ZeshuLiu/PolaMiyaHardware/结构Rev2N/电路/机身主控/TSSOP-14_4.4x5mm_P0.65mm.SLDASM

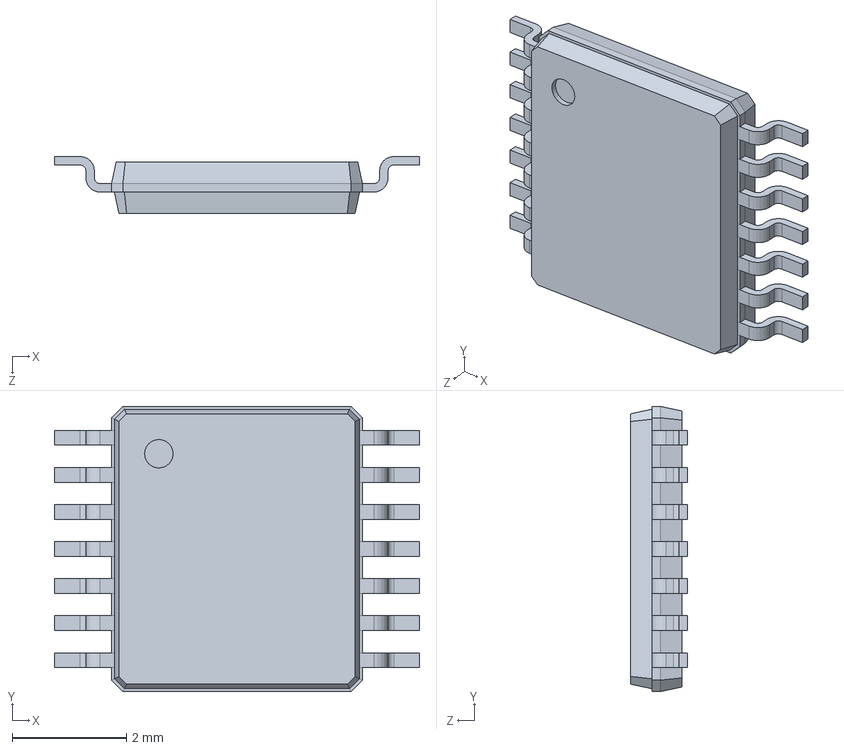
[picture p2: CAD file, 2025-09-27]
结构Rev2N/电路/机身主控/TSSOP-14_4.4x5mm_P0.65mm.SLDASM
6.40 x 5.00 x 1.00 mm
