ZeshuLiu/PolaMiyaHardware/结构Rev2N/电路/机身主控/VSSOP-8_3.0x3.0mm_P0.65mm.SLDASM

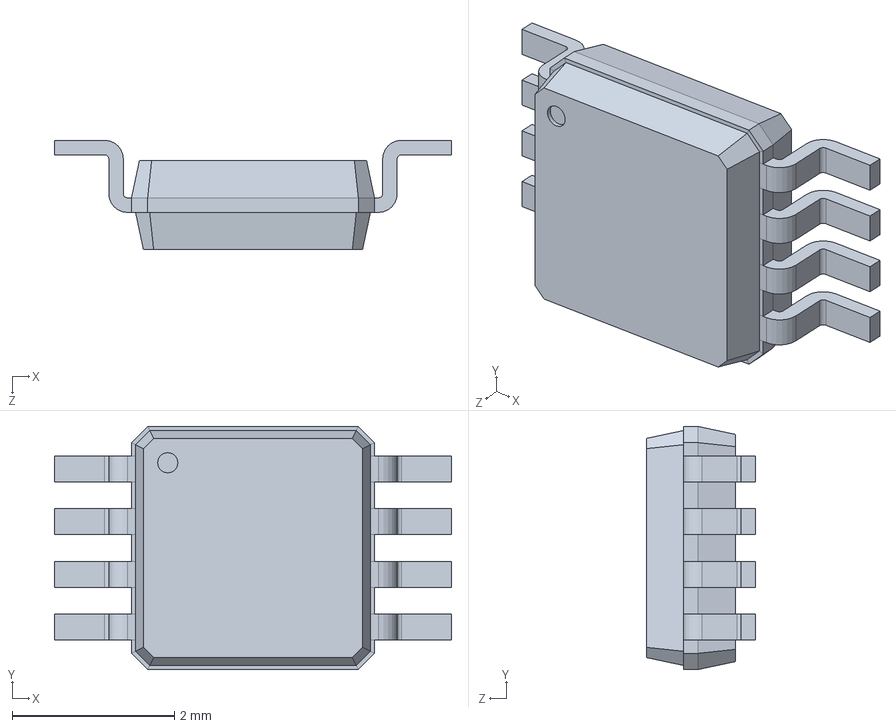
[picture p5: CAD file, 2025-09-27]
结构Rev2N/电路/机身主控/VSSOP-8_3.0x3.0mm_P0.65mm.SLDASM
4.90 x 3.00 x 1.35 mm
