ZeshuLiu/PolaMiyaHardware/电路/闪光灯转接/FlashAdapter/upper.SLDPRT

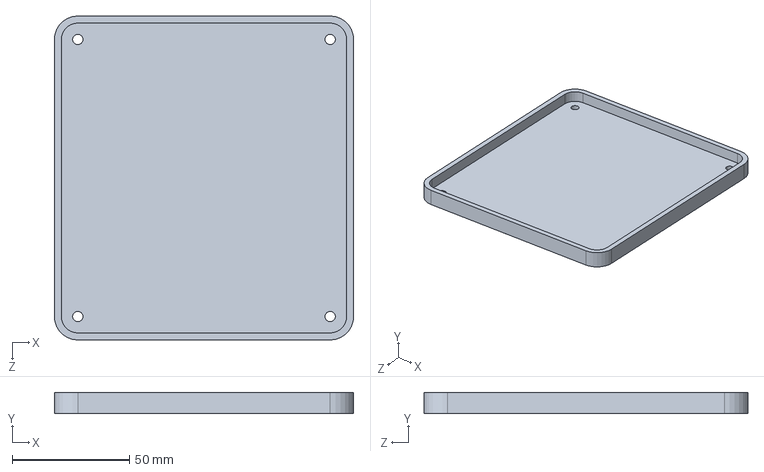
[picture p7: CAD file, 2025-12-25]
电路/闪光灯转接/FlashAdapter/upper.SLDPRT
127.5 x 9.00 x 138.0 mm
