ZeshuLiu/PolaMiyaHardware/结构Rev2N/外壳/顶壳.SLDPRT

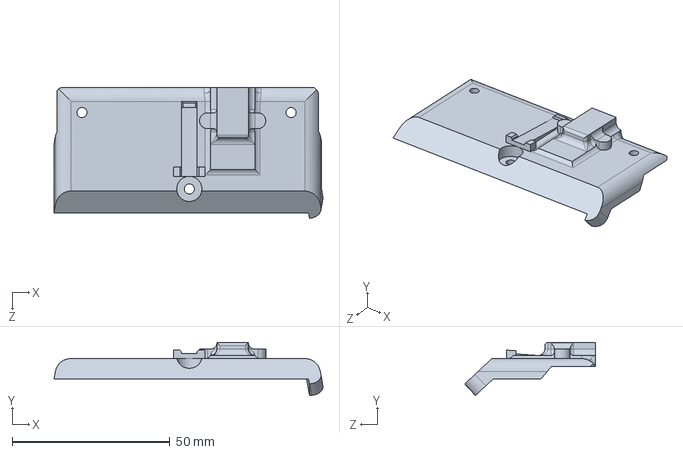
[picture p9: CAD file, 2026-03-20]
结构Rev2N/外壳/顶壳.SLDPRT
85.2 x 16.8 x 41.4 mm
