ZeshuLiu/PolaMiyaHardware/结构Rev2N/片仓总成/STP/右侧板.STEP

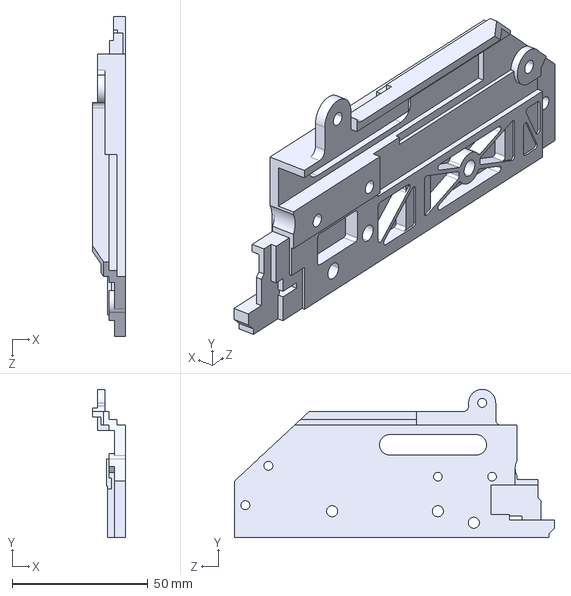
[picture p11: CAD file, 2026-03-20]
结构Rev2N/片仓总成/STP/右侧板.STEP
12.0 x 54.7 x 118.0 mm
