ZeshuLiu/PolaMiyaHardware/结构Rev2N/片仓总成/反光镜盖板.SLDPRT

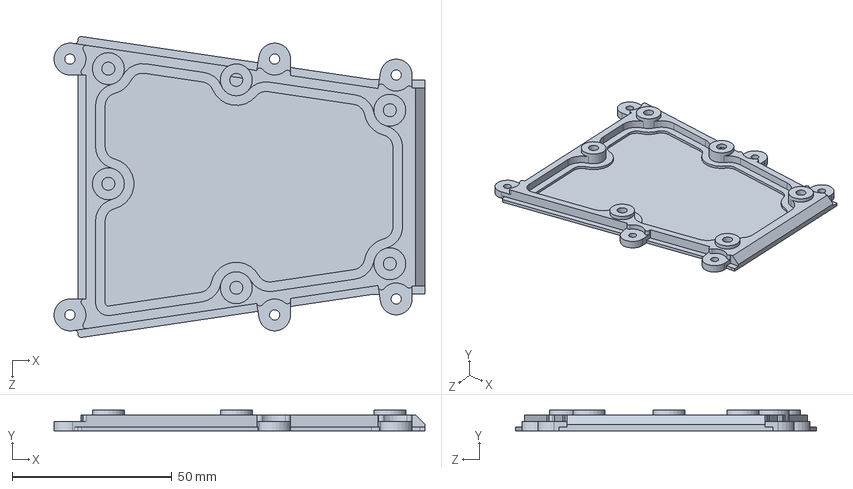
[picture p12: CAD file, 2026-03-20]
结构Rev2N/片仓总成/反光镜盖板.SLDPRT
116.0 x 6.50 x 94.1 mm
