ZeshuLiu/PolaMiyaHardware/结构Rev2N/电路/PM_Controller_R1_0/PM_Controller_Rev1_0.step

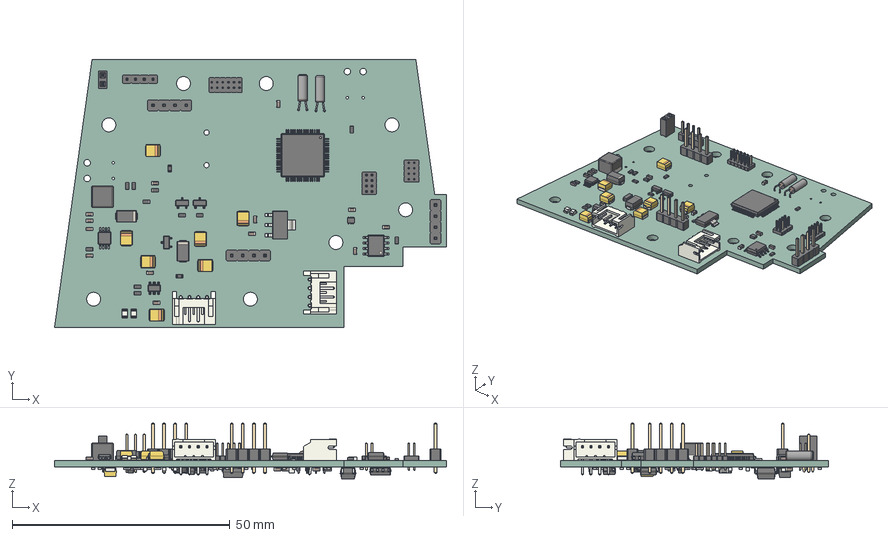
[picture p13: CAD file, 2025-06-10]
结构Rev2N/电路/PM_Controller_R1_0/PM_Controller_Rev1_0.step
90.0 x 61.5 x 12.8 mm
PinHeader_2x04_P1.27mm_Vertical x 2
R_0603_1608Metric x 42
C_0603_1608Metric x 30
SOT-23 x 6
LQFP-64_10x10mm_P0.5mm
PinHeader_1x04_P2.00mm_Vertical
PinHeader_2x06_P1.27mm_Vertical
CP_EIA-3528-21_Kemet-B x 8
PinHeader_1x04_P2.54mm_Vertical x 3
LED_0805_2012Metric x 2
SOIC-8_3.9x4.9mm_P1.27mm x 2
SOT-23-6
JST_PH_S4B-PH-K_1x04_P2.00mm_Horizontal x 2
D_SMA x 3
SOT-563
Crystal_C26-LF_D2.1mm_L6.5mm_Horizontal x 3
SOT-223
PinSocket_1x02_P2.00mm_Vertical
L_APV_ANR5040
VSSOP-8_3x3mm_P0.65mm
TSSOP-14_4.4x5mm_P0.65mm
SOT-23-5
MFSOP6-4_4.4x3.6mm_P1.27mm
L_0805_2012Metric
PM_Controller_PCB
