ZeshuLiu/PolaMiyaHardware/结构Rev2N/电路/电机驱动/PH2x4.SLDPRT

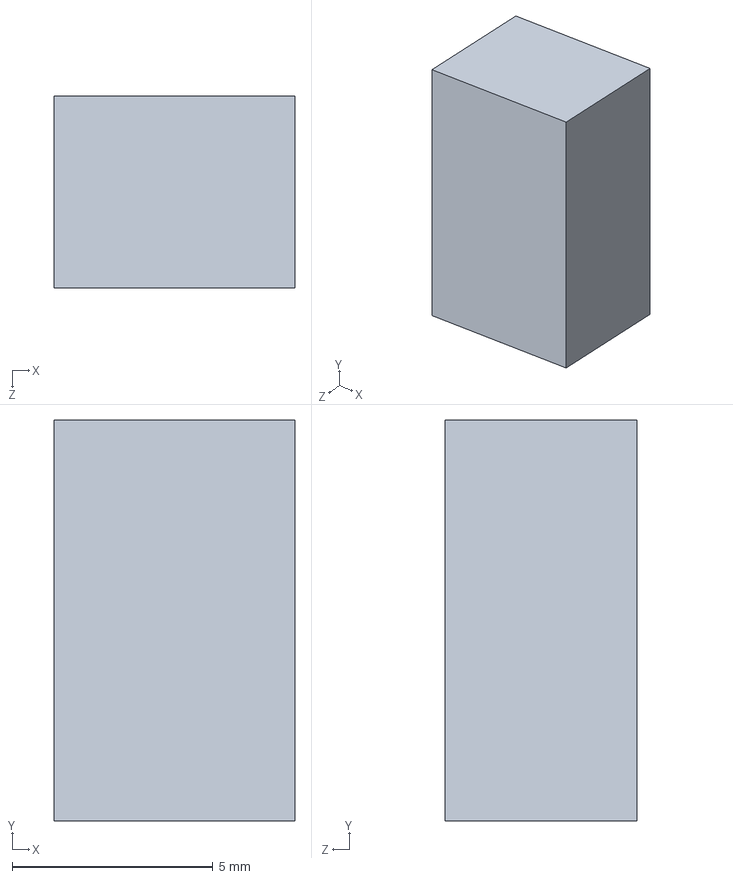
[picture p14: CAD file, 2026-02-14]
结构Rev2N/电路/电机驱动/PH2x4.SLDPRT
6.00 x 10.0 x 4.80 mm
