ZeshuLiu/PolaMiyaHardware/结构Rev2N/电路/闪光灯.SLDPRT

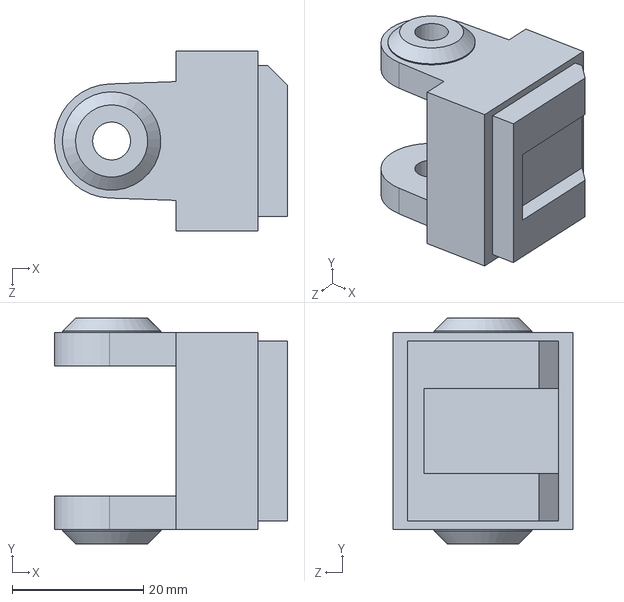
[picture p15: CAD file, 2025-12-25]
结构Rev2N/电路/闪光灯.SLDPRT
35.5 x 34.4 x 27.5 mm
