ZeshuLiu/PolaMiyaHardware/结构Rev2N/镜头总成/STP/滑块连接.STEP

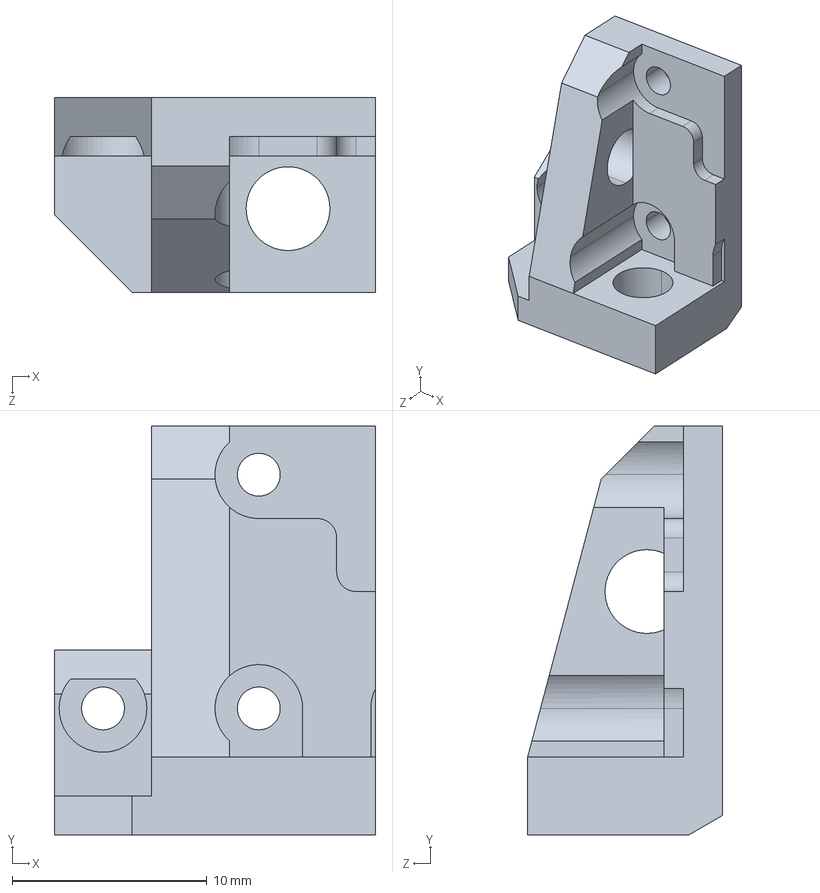
[picture p16: CAD file, 2026-03-20]
结构Rev2N/镜头总成/STP/滑块连接.STEP
16.5 x 21.0 x 10.0 mm
