ZeshuLiu/PolaMiyaHardware/结构Rev2N/外壳/左侧壳.SLDPRT

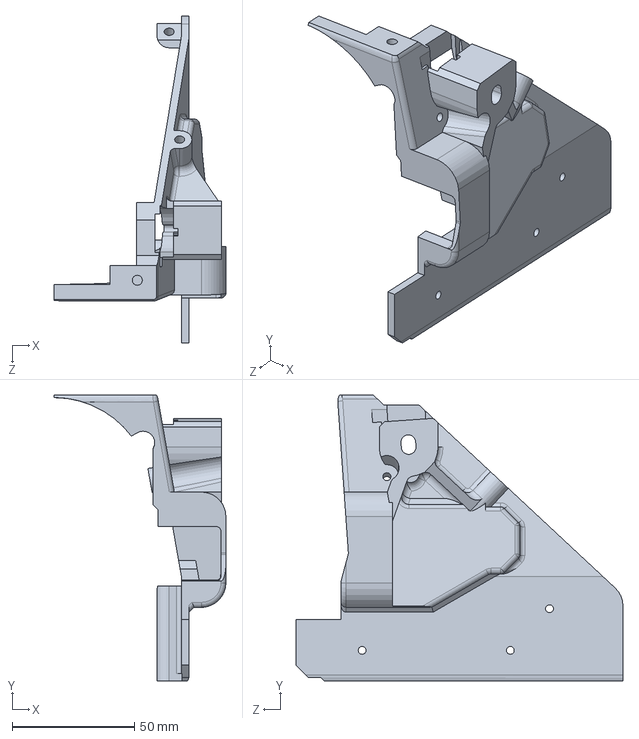
[picture p20: CAD file, 2026-03-20]
结构Rev2N/外壳/左侧壳.SLDPRT
70.2 x 116.7 x 133.5 mm
