ZeshuLiu/PolaMiyaHardware/结构Rev2N/片仓总成/STP/底板.STEP

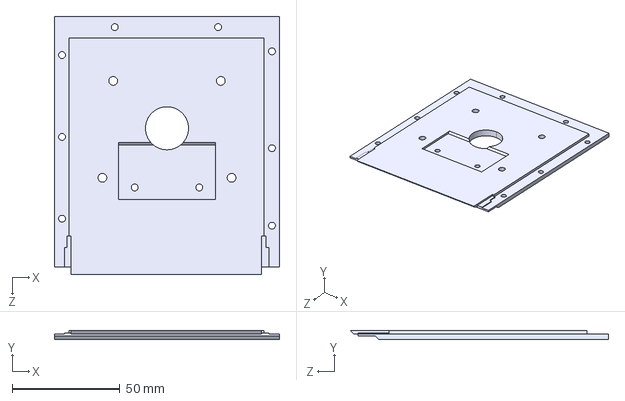
[picture p22: CAD file, 2026-03-20]
结构Rev2N/片仓总成/STP/底板.STEP
104.5 x 4.00 x 120.0 mm
