ZeshuLiu/PolaMiyaHardware/结构Rev2N/电路/激光测距SDM18.SLDPRT

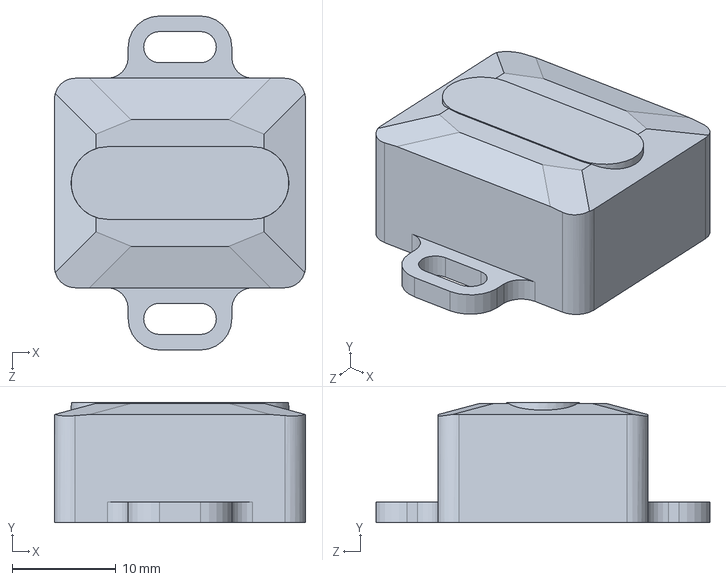
[picture p24: CAD file, 2025-09-27]
结构Rev2N/电路/激光测距SDM18.SLDPRT
24.2 x 11.6 x 32.2 mm
