ZeshuLiu/PolaMiyaHardware/结构Rev2N/电路/电机驱动/MotroDrive.step

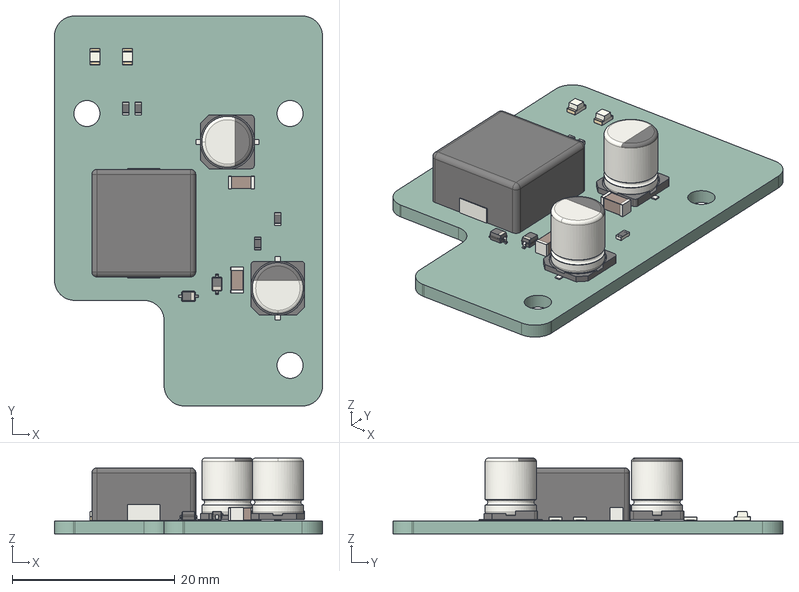
[picture p25: CAD file, 2025-06-10]
结构Rev2N/电路/电机驱动/MotroDrive.step
33.0 x 48.0 x 9.35 mm
D_SOD_323 x 2
CP_Elec_63x77 x 2
C_1206_3216Metric x 2
R_0603_1608Metric x 4
LED_0805_2012Metric x 2
L_APV_APH1265
_autosave-MotroDrive_PCB
