ZeshuLiu/PolaMiyaHardware/结构Rev2N/镜头总成/STP/MamiyaPressLensSeat.STEP

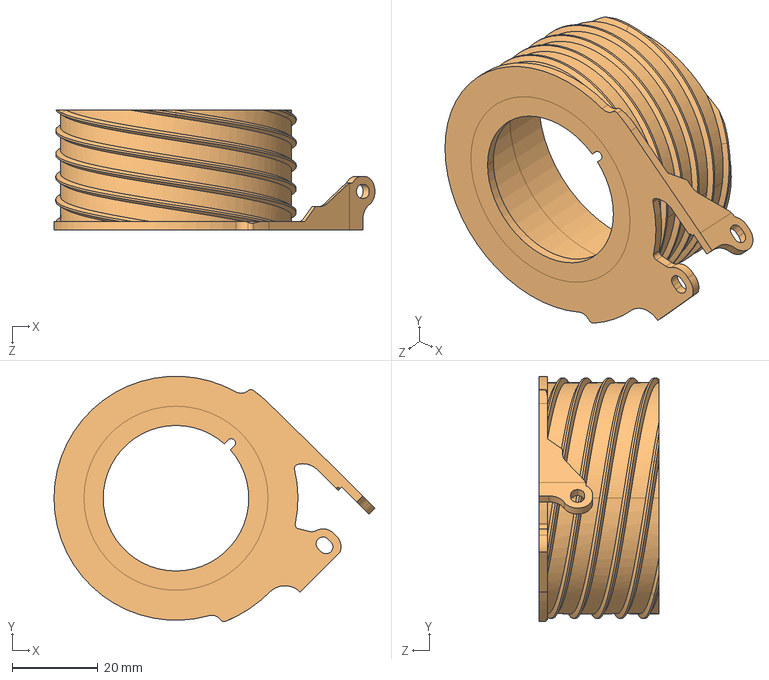
[picture p26: CAD file, 2025-12-25]
结构Rev2N/镜头总成/STP/MamiyaPressLensSeat.STEP
75.0 x 57.3 x 28.0 mm
