ZeshuLiu/PolaMiyaHardware/结构Rev2N/镜头总成/镜头衬垫.SLDPRT

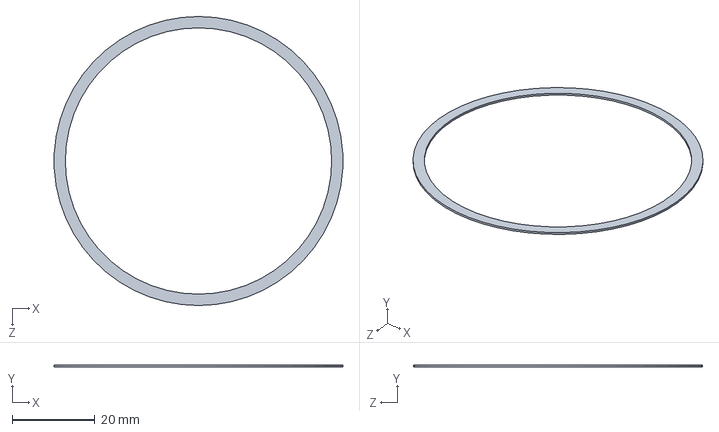
[picture p27: CAD file, 2026-03-20]
结构Rev2N/镜头总成/镜头衬垫.SLDPRT
69.9 x 0.5 x 70.0 mm
