ZeshuLiu/PolaMiyaHardware/结构Rev2N/全息取景器/主座.SLDPRT

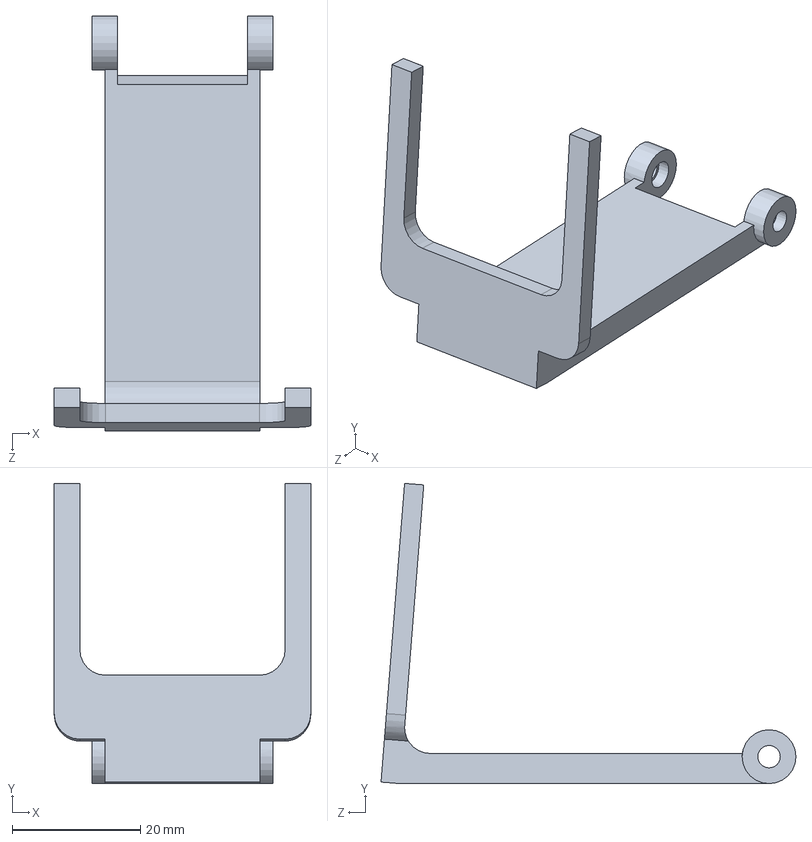
[picture p28: CAD file, 2026-03-20]
结构Rev2N/全息取景器/主座.SLDPRT
40.0 x 46.8 x 64.7 mm
