ZeshuLiu/PolaMiyaHardware/结构Rev2N/外壳/背壳.SLDPRT

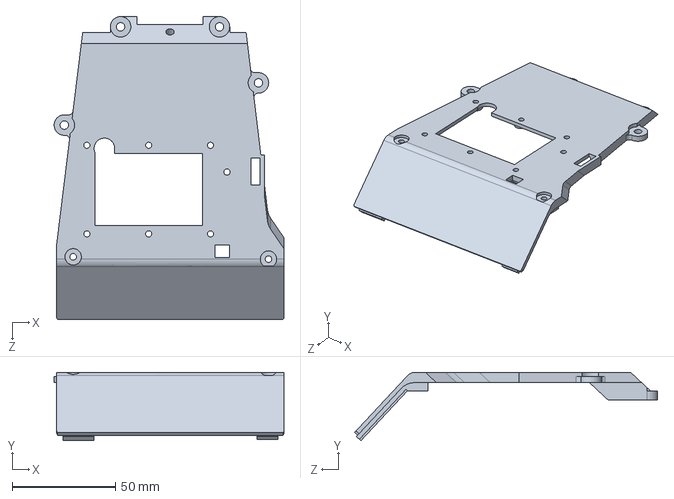
[picture p29: CAD file, 2026-02-14]
结构Rev2N/外壳/背壳.SLDPRT
111.6 x 33.2 x 147.0 mm
