ZeshuLiu/PolaMiyaHardware/结构Rev2N/片仓总成/STP/左侧板.STEP

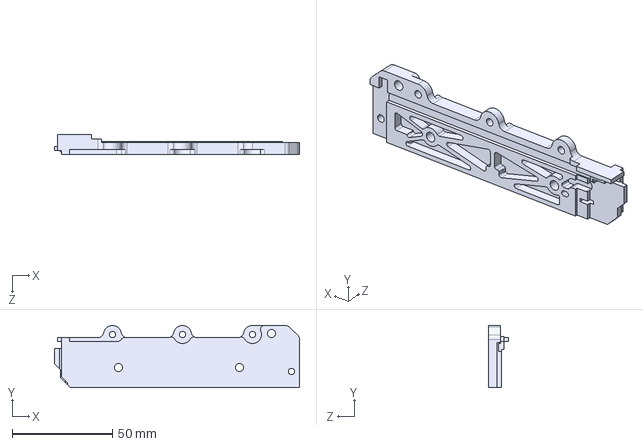
[picture p31: CAD file, 2026-03-20]
结构Rev2N/片仓总成/STP/左侧板.STEP
122.5 x 31.0 x 10.0 mm
