ZeshuLiu/PolaMiyaHardware/结构Rev2N/片仓总成/调焦桶盖.SLDPRT

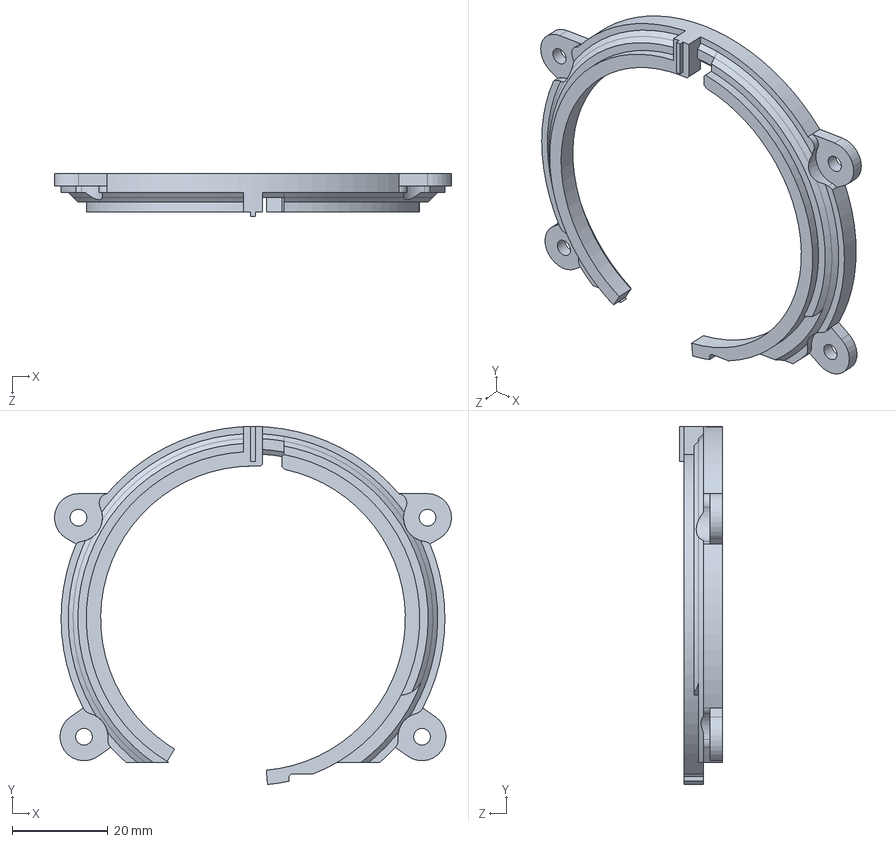
[picture p32: CAD file, 2026-03-20]
结构Rev2N/片仓总成/调焦桶盖.SLDPRT
82.7 x 74.6 x 9.00 mm
