ZeshuLiu/PolaMiyaHardware/结构Rev2N/电路/电池按钮.SLDPRT

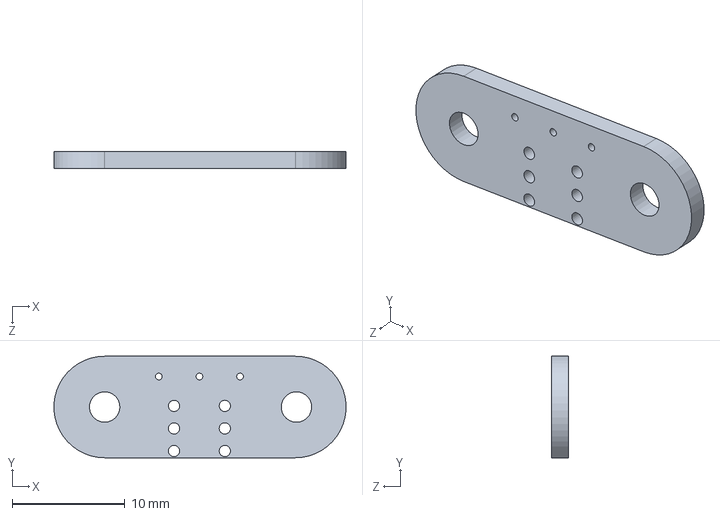
[picture p33: CAD file, 2025-09-27]
结构Rev2N/电路/电池按钮.SLDPRT
25.9 x 9.00 x 1.51 mm
