ZeshuLiu/PolaMiyaHardware/结构Rev2N/镜头总成/内环.SLDPRT

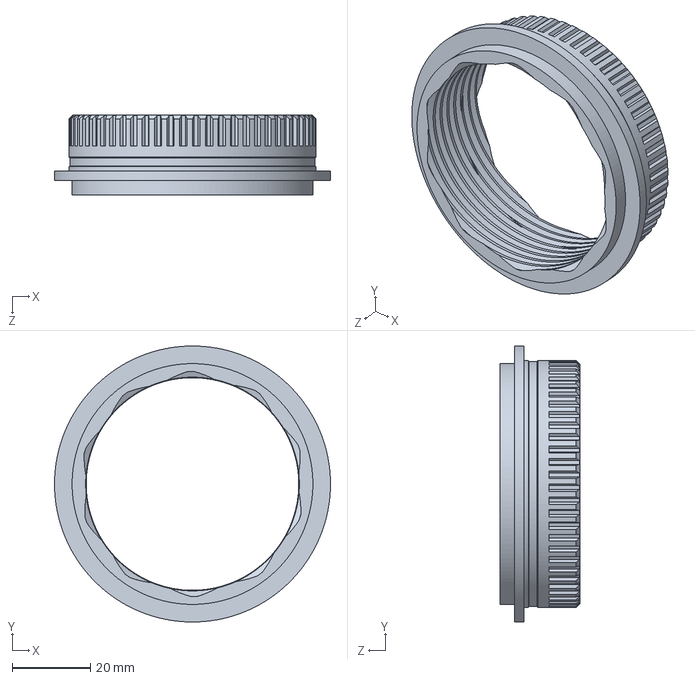
[picture p34: CAD file, 2026-03-20]
结构Rev2N/镜头总成/内环.SLDPRT
70.5 x 70.5 x 20.5 mm
