ZeshuLiu/PolaMiyaHardware/结构Rev2N/全息取景器/反射镜片.SLDPRT

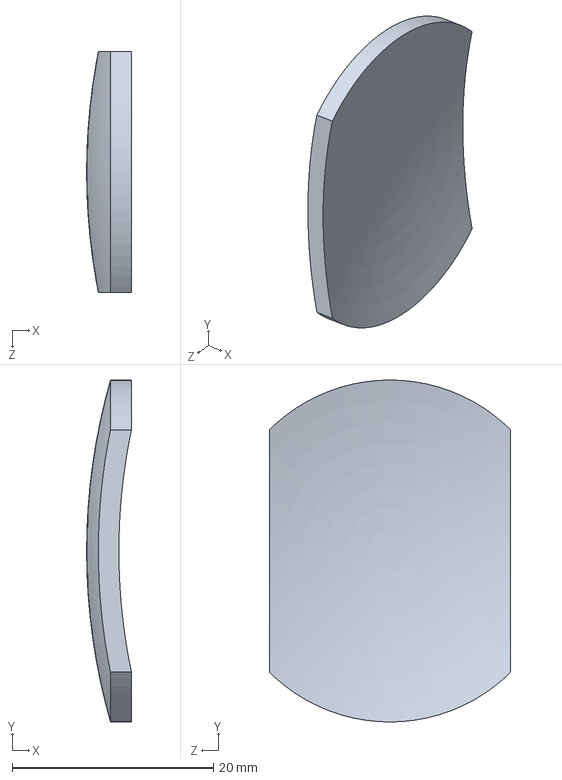
[picture p35: CAD file, 2026-03-20]
结构Rev2N/全息取景器/反射镜片.SLDPRT
4.46 x 34.0 x 24.0 mm
