ZeshuLiu/PolaMiyaHardware/结构Rev2N/外壳/屏幕壳子.SLDPRT

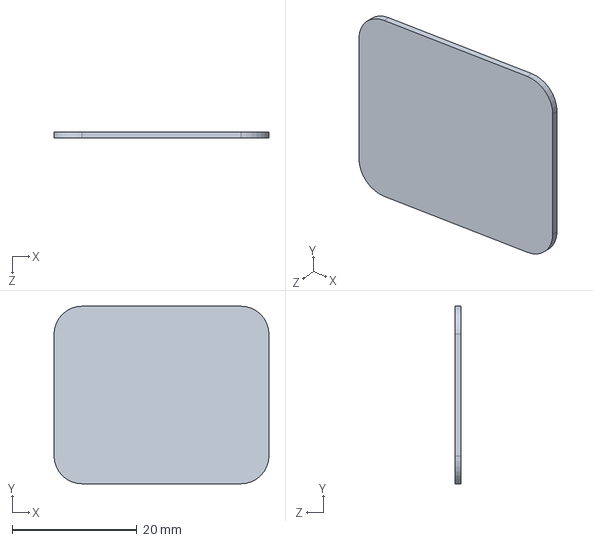
[picture p36: CAD file, 2026-01-21]
结构Rev2N/外壳/屏幕壳子.SLDPRT
34.5 x 28.5 x 1.00 mm
