ZeshuLiu/PolaMiyaHardware/结构Rev2N/消光绒模板/后侧.SLDPRT

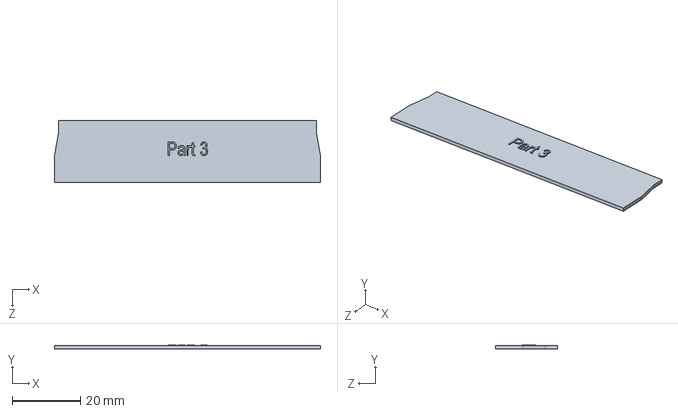
[picture p37: CAD file, 2025-09-27]
结构Rev2N/消光绒模板/后侧.SLDPRT
78.0 x 1.20 x 18.1 mm
