ZeshuLiu/PolaMiyaHardware/结构Rev2N/片仓总成/STP/主片仓.STEP

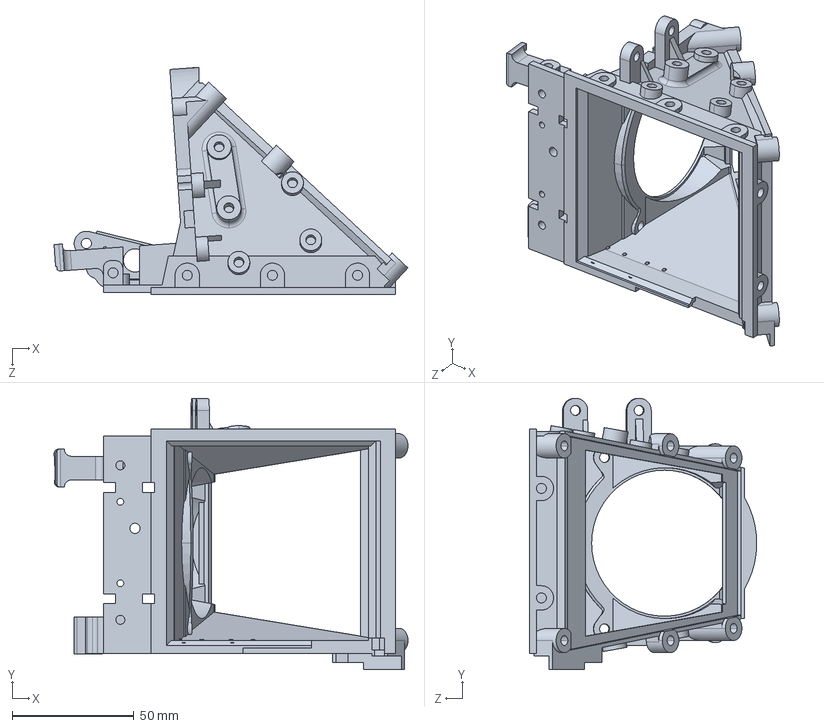
[picture p38: CAD file, 2025-12-25]
结构Rev2N/片仓总成/STP/主片仓.STEP
145.5 x 111.6 x 93.5 mm
