ZeshuLiu/PolaMiyaHardware/结构Rev2N/片仓总成/后侧板.SLDPRT

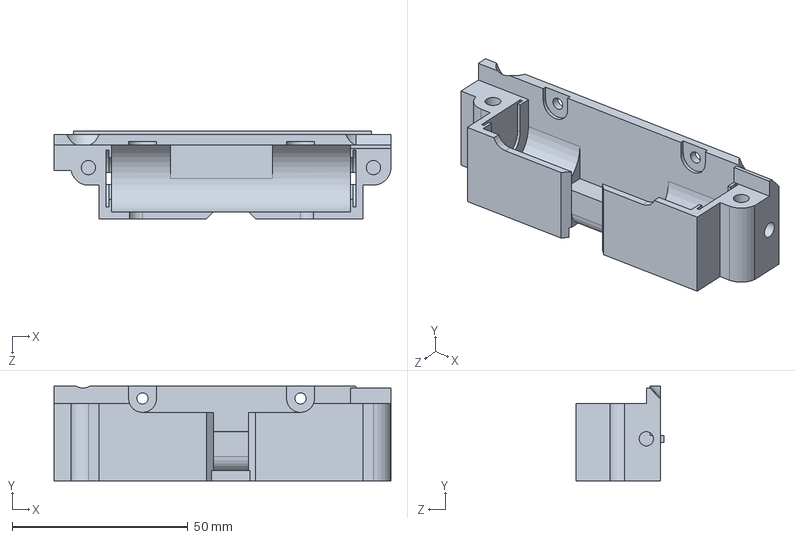
[picture p39: CAD file, 2026-03-20]
结构Rev2N/片仓总成/后侧板.SLDPRT
96.0 x 27.0 x 25.0 mm
