ZeshuLiu/PolaMiyaHardware/结构Rev2N/电路/DispKey_R1_0/DispKey_PCB.SLDPRT

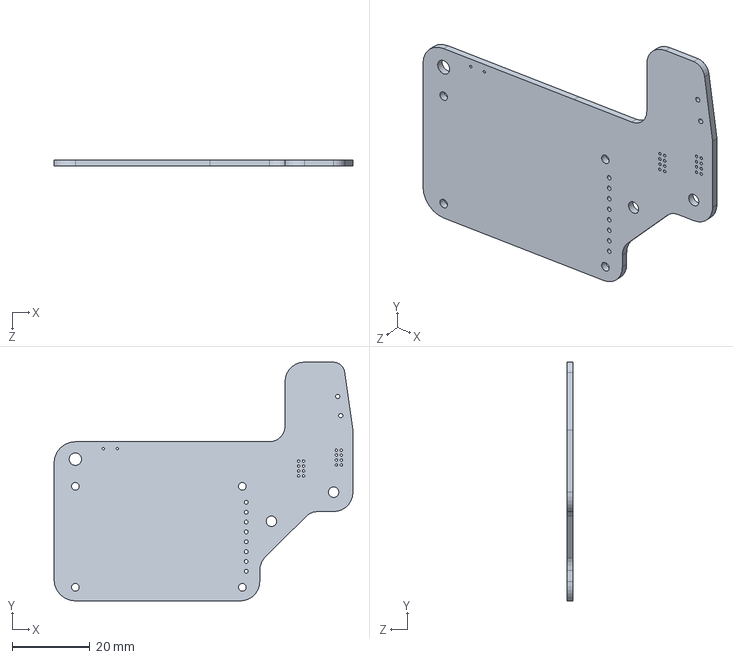
[picture p40: CAD file, 2025-09-27]
结构Rev2N/电路/DispKey_R1_0/DispKey_PCB.SLDPRT
77.0 x 61.5 x 1.51 mm
