ZeshuLiu/PolaMiyaHardware/结构Rev2N/电路/大头拨轮.SLDPRT

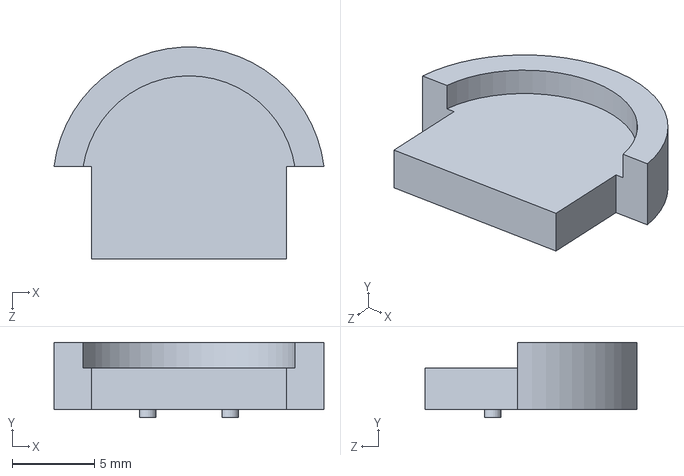
[picture p41: CAD file, 2025-09-27]
结构Rev2N/电路/大头拨轮.SLDPRT
16.4 x 4.55 x 12.8 mm
