ZeshuLiu/PolaMiyaHardware/结构Rev2N/镜头总成/挡板.SLDPRT

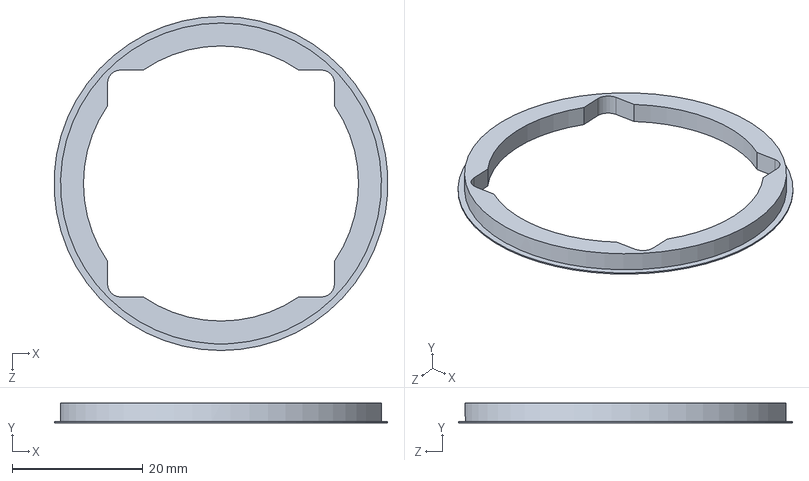
[picture p42: CAD file, 2025-09-27]
结构Rev2N/镜头总成/挡板.SLDPRT
50.9 x 3.00 x 51.0 mm
