ZeshuLiu/PolaMiyaHardware/结构Rev2N/外壳/屏幕盖.SLDPRT

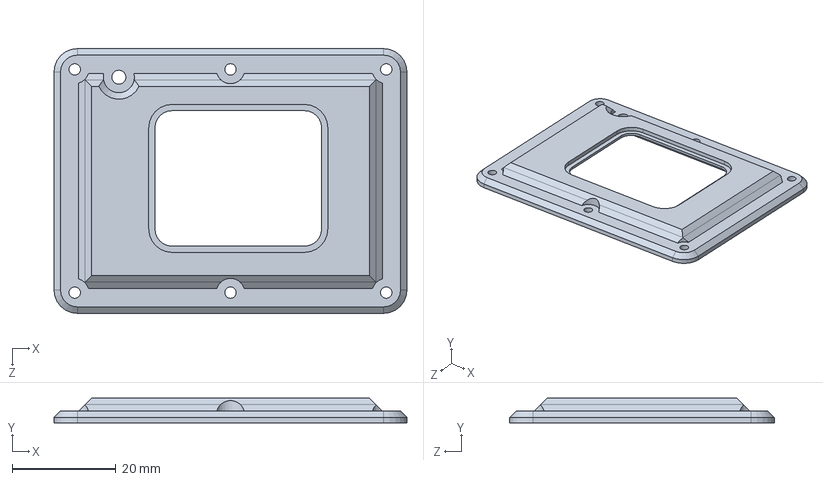
[picture p43: CAD file, 2026-01-21]
结构Rev2N/外壳/屏幕盖.SLDPRT
68.0 x 4.81 x 51.0 mm
