ZeshuLiu/PolaMiyaHardware/结构Rev2N/消光绒模板/右内壁.SLDPRT

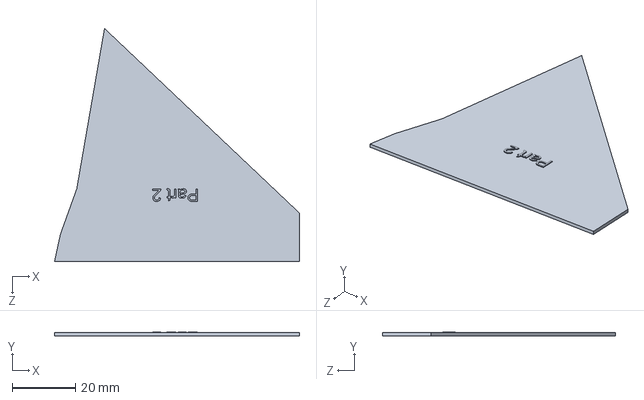
[picture p44: CAD file, 2025-09-27]
结构Rev2N/消光绒模板/右内壁.SLDPRT
77.8 x 1.20 x 74.0 mm
