ZeshuLiu/PolaMiyaHardware/结构Rev2N/电路/1.69寸彩色TFT.SLDPRT

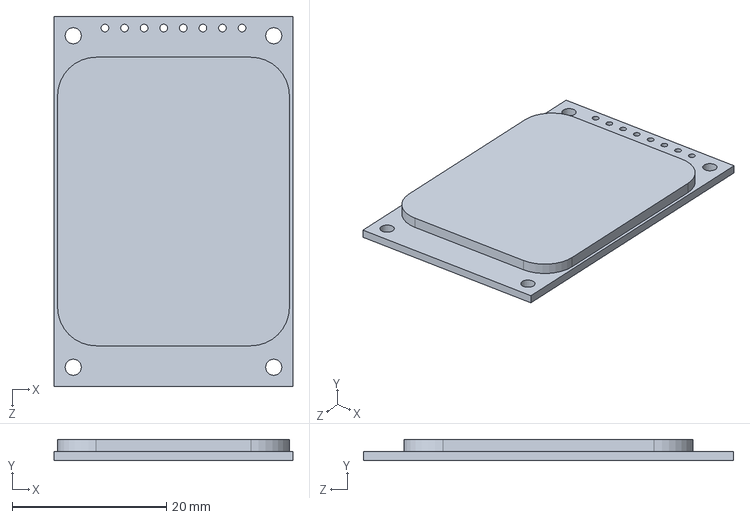
[picture p45: CAD file, 2025-09-27]
结构Rev2N/电路/1.69寸彩色TFT.SLDPRT
31.0 x 2.76 x 48.0 mm
