ZeshuLiu/PolaMiyaHardware/结构Rev2N/镜头总成/闪光灯线.SLDPRT

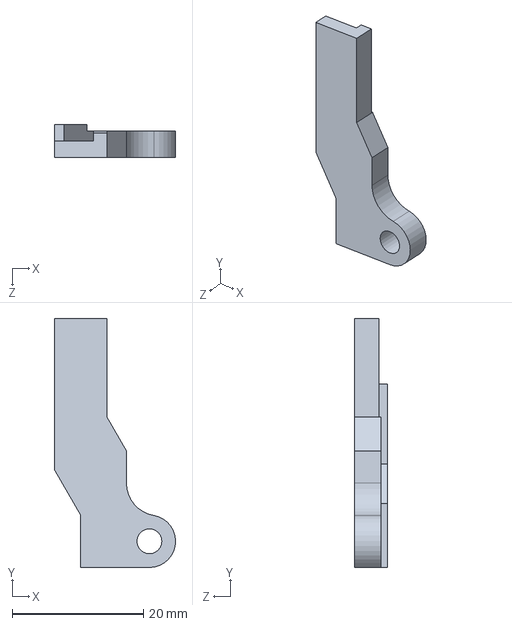
[picture p46: CAD file, 2025-09-27]
结构Rev2N/镜头总成/闪光灯线.SLDPRT
18.5 x 38.0 x 5.00 mm
