ZeshuLiu/PolaMiyaHardware/结构Rev2N/外壳/右侧壳.SLDPRT

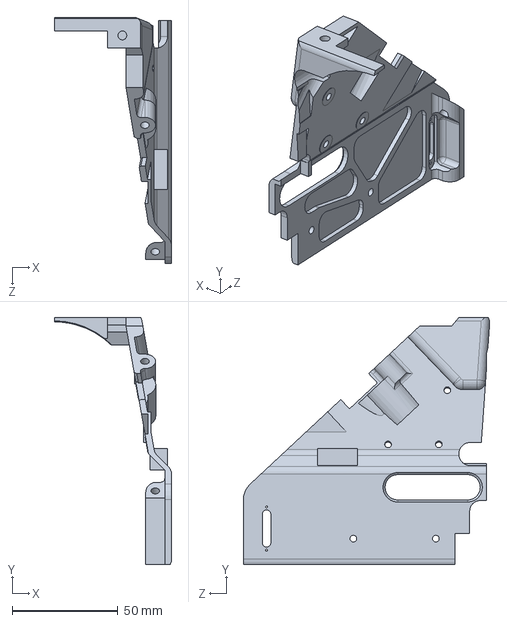
[picture p47: CAD file, 2025-12-25]
结构Rev2N/外壳/右侧壳.SLDPRT
55.4 x 116.8 x 116.4 mm
