ZeshuLiu/PolaMiyaHardware/结构Rev2N/片仓总成/电池压板.SLDPRT

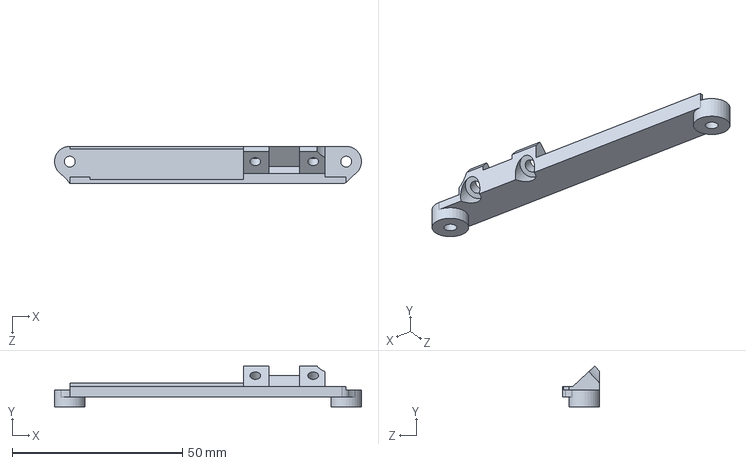
[picture p48: CAD file, 2025-09-27]
结构Rev2N/片仓总成/电池压板.SLDPRT
90.2 x 12.0 x 11.0 mm
