ZeshuLiu/PolaMiyaHardware/结构Rev2N/电路/7x7按键.SLDPRT

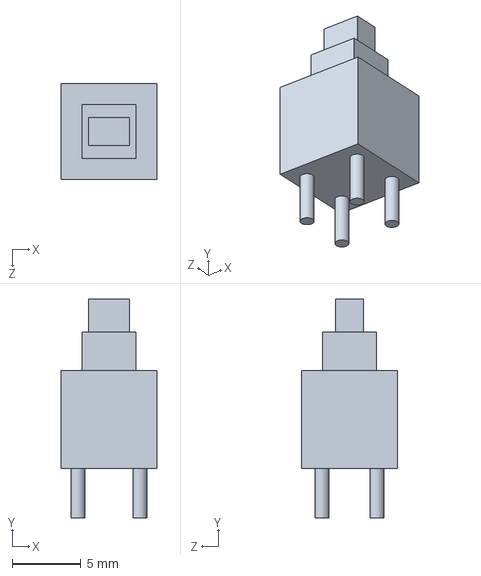
[picture p49: CAD file, 2025-09-27]
结构Rev2N/电路/7x7按键.SLDPRT
7.00 x 15.9 x 7.00 mm
