ZeshuLiu/PolaMiyaHardware/结构Rev2N/电路/机身主控/C_0805_2012Metric-3.SLDPRT

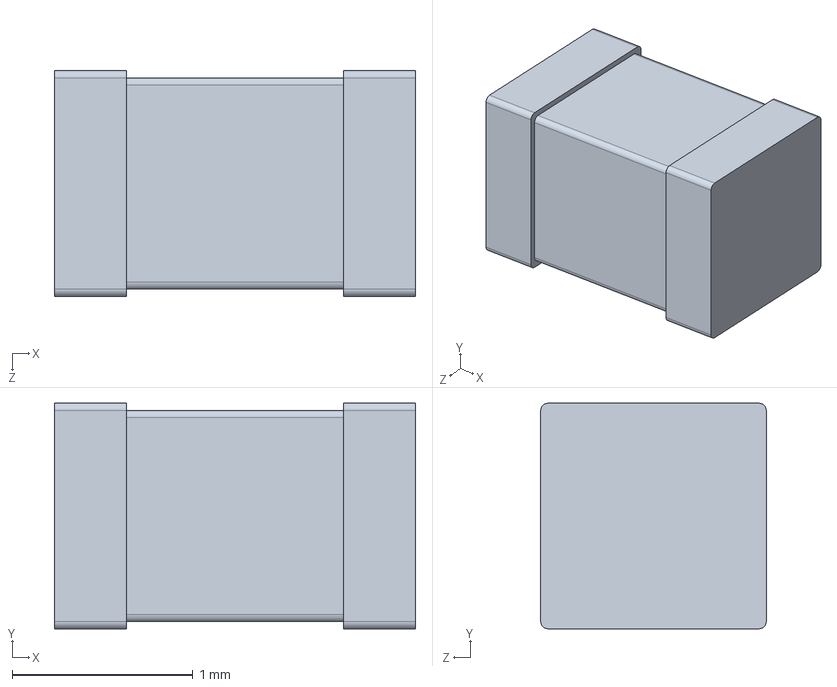
[picture p50: CAD file, 2025-09-27]
结构Rev2N/电路/机身主控/C_0805_2012Metric-3.SLDPRT
2.00 x 1.25 x 1.25 mm
