ZeshuLiu/PolaMiyaHardware/结构Rev2N/镜头总成/挡片测试.SLDPRT

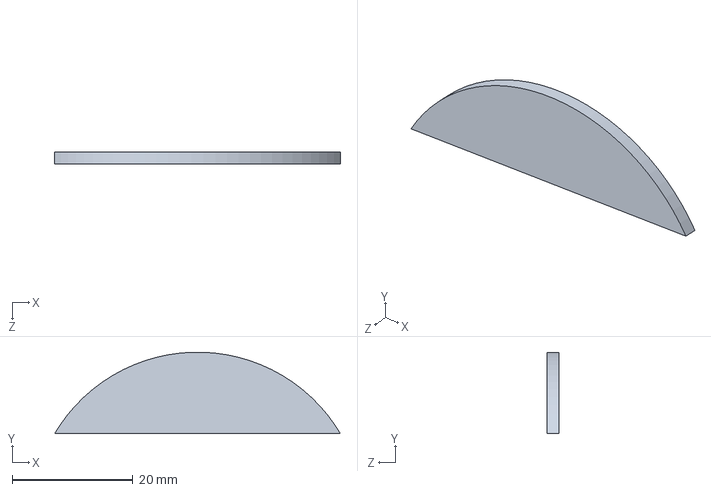
[picture p51: CAD file, 2025-09-27]
结构Rev2N/镜头总成/挡片测试.SLDPRT
47.3 x 13.5 x 2.00 mm
