ZeshuLiu/PolaMiyaHardware/结构Rev2N/外壳/镜头挡光板.SLDPRT

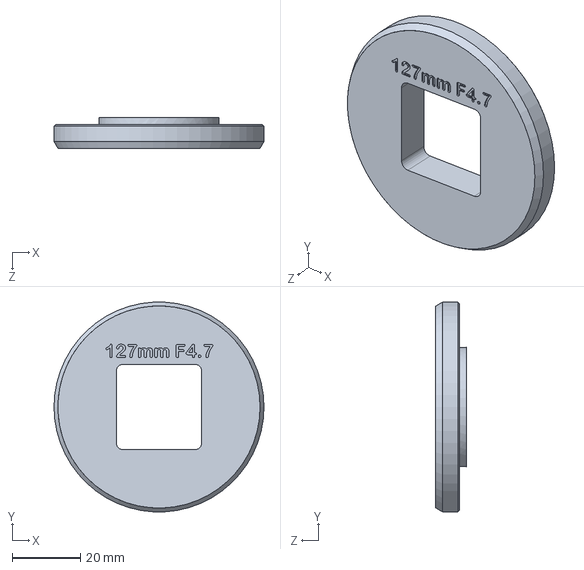
[picture p52: CAD file, 2025-11-23]
结构Rev2N/外壳/镜头挡光板.SLDPRT
61.5 x 61.4 x 9.00 mm
