ZeshuLiu/PolaMiyaHardware/结构Rev2N/片仓总成/主片仓Test4.SLDPRT

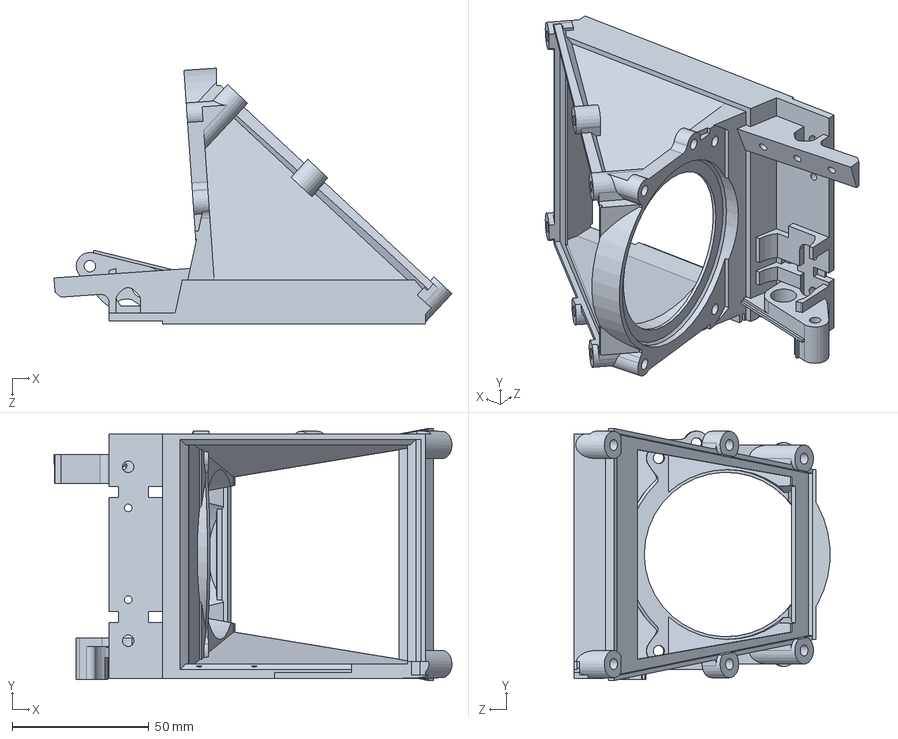
[picture p53: CAD file, 2025-09-27]
结构Rev2N/片仓总成/主片仓Test4.SLDPRT
145.3 x 92.1 x 93.4 mm
