ZeshuLiu/PolaMiyaHardware/结构Rev2N/电路/机身主控/L_Cenker_CKCS4020-7.SLDPRT

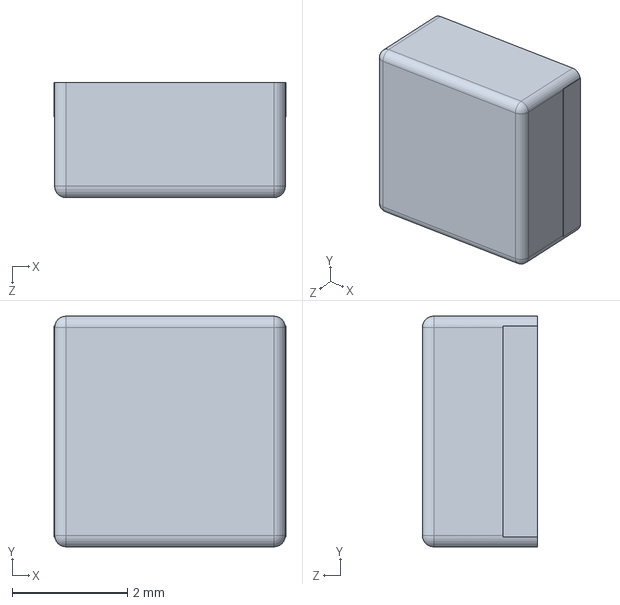
[picture p54: CAD file, 2025-09-27]
结构Rev2N/电路/机身主控/L_Cenker_CKCS4020-7.SLDPRT
4.02 x 4.00 x 2.00 mm
