ZeshuLiu/PolaMiyaHardware/结构Rev2N/电路/电池负极弹片.SLDPRT

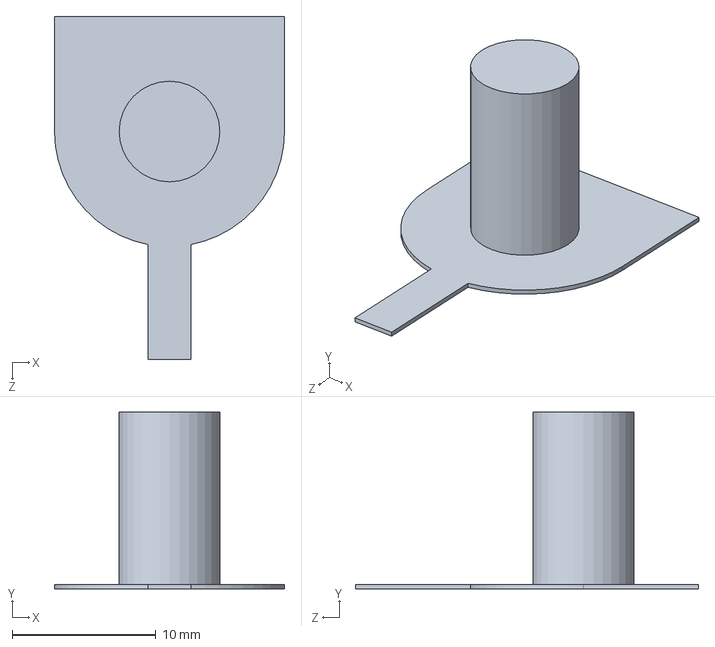
[picture p55: CAD file, 2025-09-27]
结构Rev2N/电路/电池负极弹片.SLDPRT
16.0 x 12.3 x 23.9 mm
