ZeshuLiu/PolaMiyaHardware/结构Rev2N/镜头总成/MamiyaPress127.SLDPRT

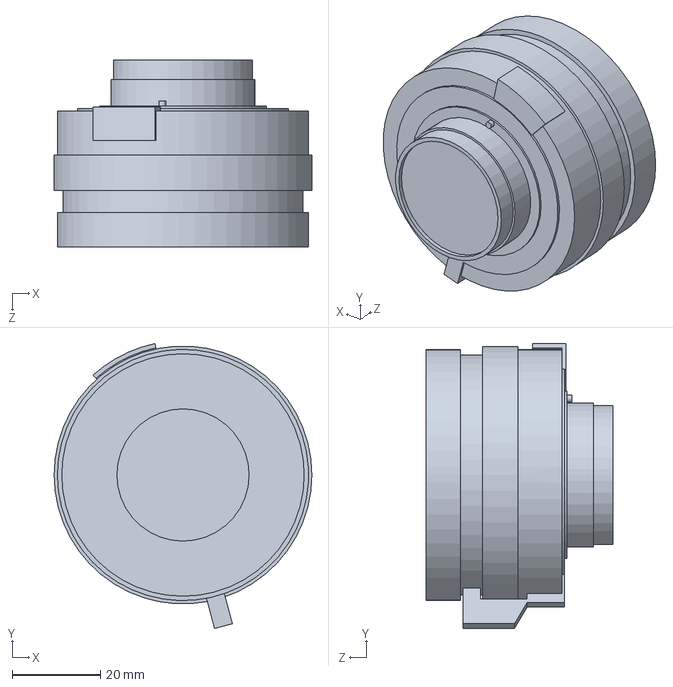
[picture p56: CAD file, 2025-09-27]
结构Rev2N/镜头总成/MamiyaPress127.SLDPRT
58.5 x 64.7 x 42.5 mm
