ZeshuLiu/PolaMiyaHardware/结构Rev2N/外壳/按钮.SLDPRT

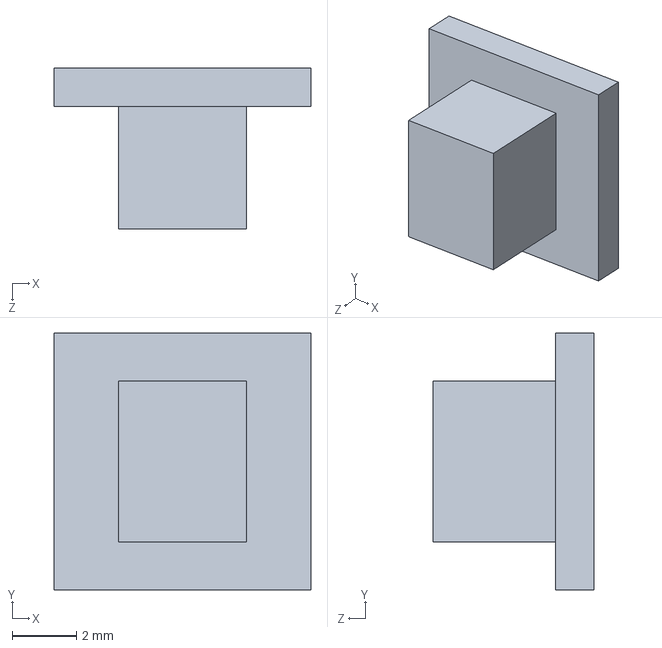
[picture p57: CAD file, 2025-09-27]
结构Rev2N/外壳/按钮.SLDPRT
8.00 x 8.00 x 5.00 mm
