ZeshuLiu/PolaMiyaHardware/结构Rev2N/片仓总成/前左盖.SLDPRT

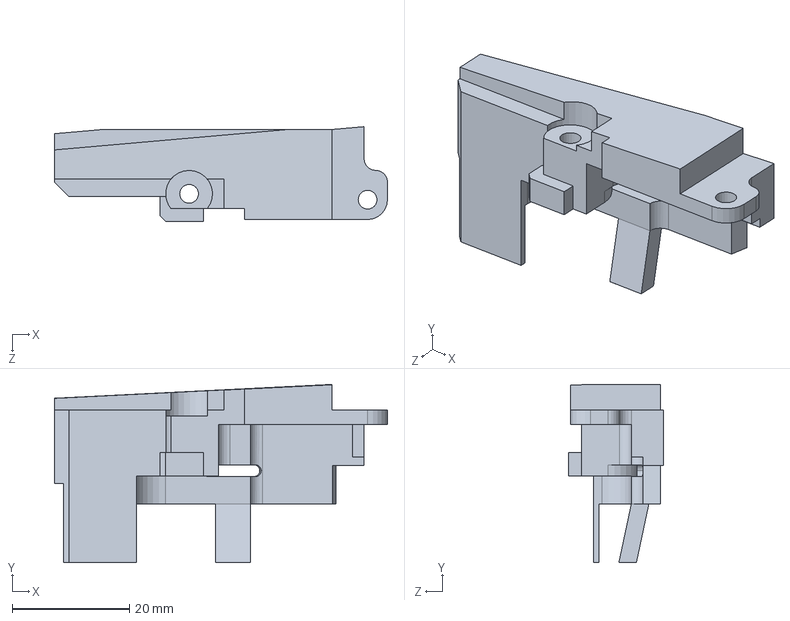
[picture p58: CAD file, 2025-09-27]
结构Rev2N/片仓总成/前左盖.SLDPRT
56.9 x 30.4 x 16.2 mm
