ZeshuLiu/PolaMiyaHardware/结构Rev2N/电路/DispKey_R1_0/DispKeyR1_0.step

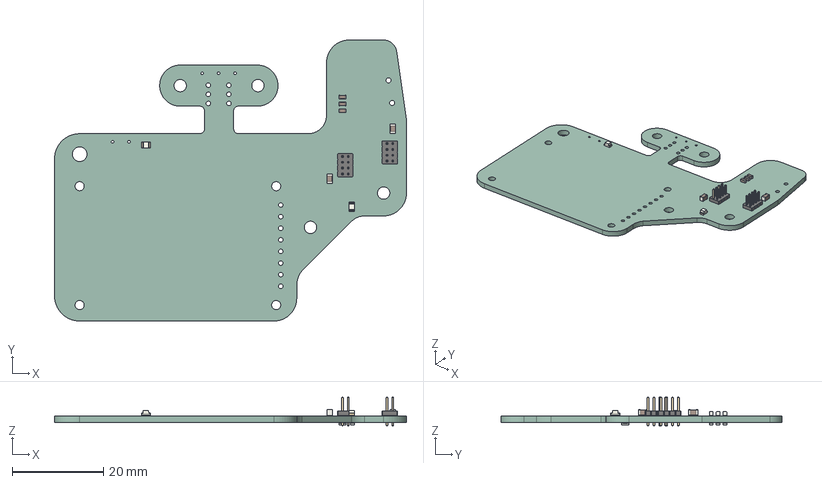
[picture p59: CAD file, 2025-06-10]
结构Rev2N/电路/DispKey_R1_0/DispKeyR1_0.step
77.0 x 61.5 x 6.30 mm
LED_0805_2012Metric x 2
C_0805_2012Metric x 2
C_0603_1608Metric x 3
PinHeader_2x04_P1.27mm_Vertical x 2
R_0603_1608Metric x 4
DispKey_PCB
