ZeshuLiu/PolaMiyaHardware/结构Rev2N/电路/机身主控/R_0603_1608Metric-0.SLDPRT

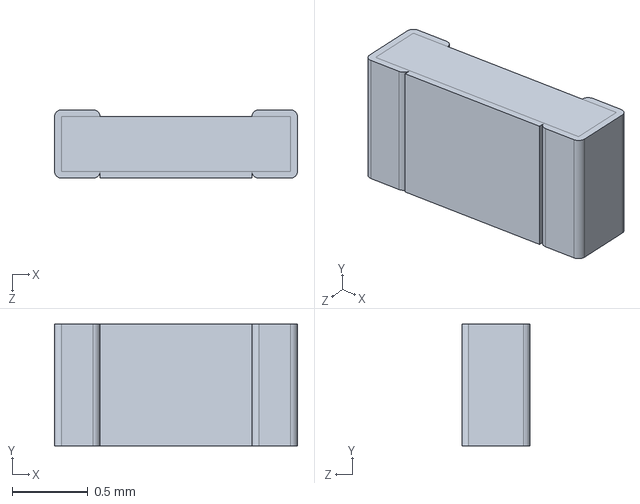
[picture p60: CAD file, 2025-09-27]
结构Rev2N/电路/机身主控/R_0603_1608Metric-0.SLDPRT
1.60 x 0.8 x 0.45 mm
