ZeshuLiu/PolaMiyaHardware/结构Rev2N/电路/电池正极弹片.SLDPRT

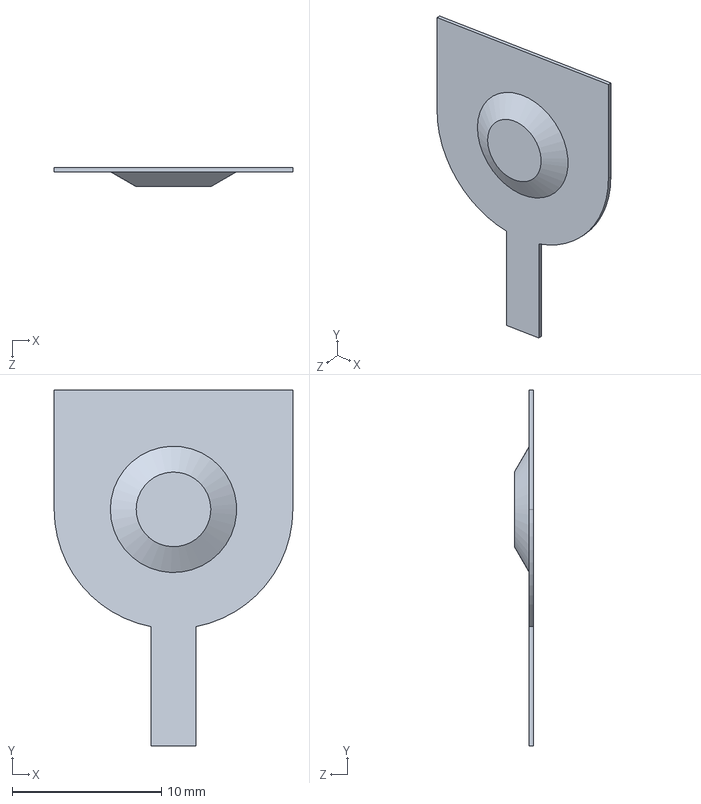
[picture p61: CAD file, 2025-09-27]
结构Rev2N/电路/电池正极弹片.SLDPRT
16.0 x 23.9 x 1.30 mm
