ZeshuLiu/PolaMiyaHardware/结构Rev2N/镜头总成/MGN7导轨1.SLDPRT

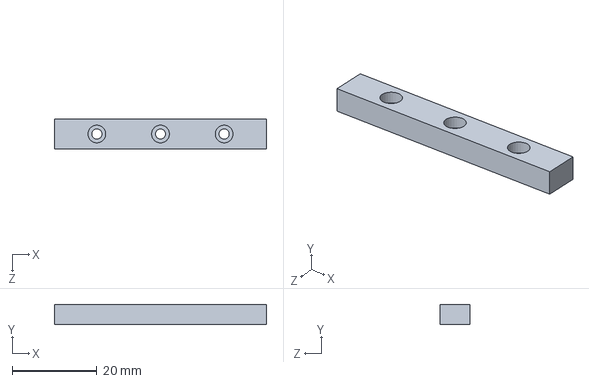
[picture p62: CAD file, 2025-09-27]
结构Rev2N/镜头总成/MGN7导轨1.SLDPRT
50.0 x 4.80 x 7.00 mm
