ZeshuLiu/PolaMiyaHardware/结构Rev2N/外壳/底壳.SLDPRT

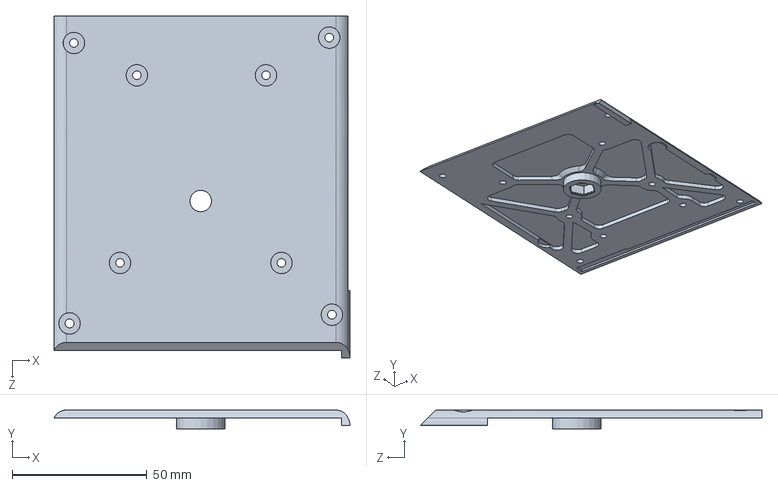
[picture p63: CAD file, 2025-09-27]
结构Rev2N/外壳/底壳.SLDPRT
110.0 x 7.00 x 127.0 mm
