ZeshuLiu/PolaMiyaHardware/结构Rev2N/片仓总成/齿轮E-拆机.SLDPRT

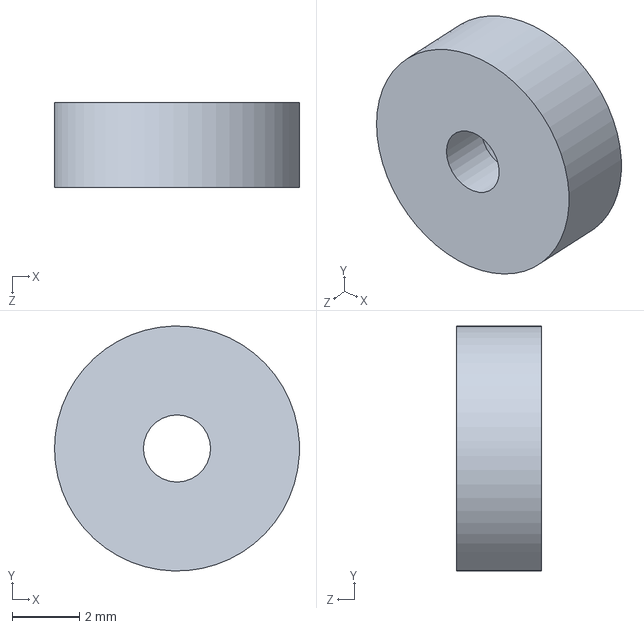
[picture p64: CAD file, 2025-09-27]
结构Rev2N/片仓总成/齿轮E-拆机.SLDPRT
7.30 x 7.30 x 2.54 mm
