ZeshuLiu/PolaMiyaHardware/结构Rev2N/镜头总成/MGN7C.SLDPRT

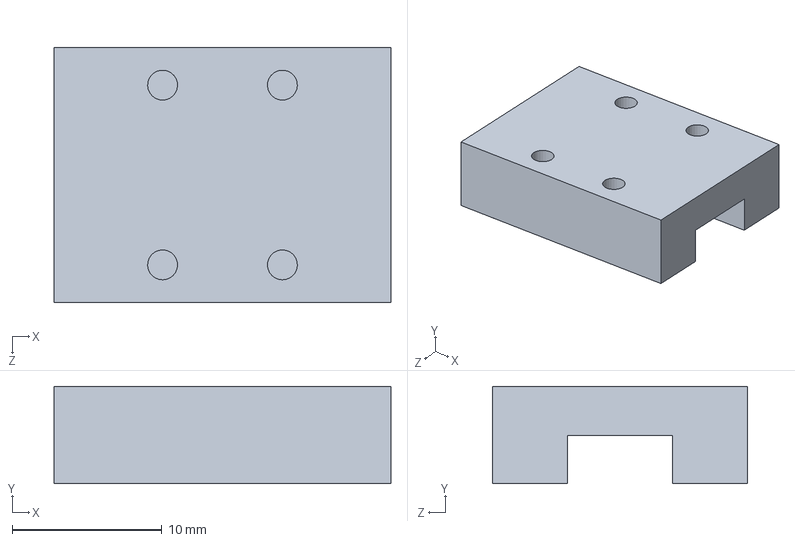
[picture p65: CAD file, 2025-09-27]
结构Rev2N/镜头总成/MGN7C.SLDPRT
22.5 x 6.50 x 17.0 mm
