ZeshuLiu/PolaMiyaHardware/结构Rev2N/外壳/推片杆外罩.SLDPRT

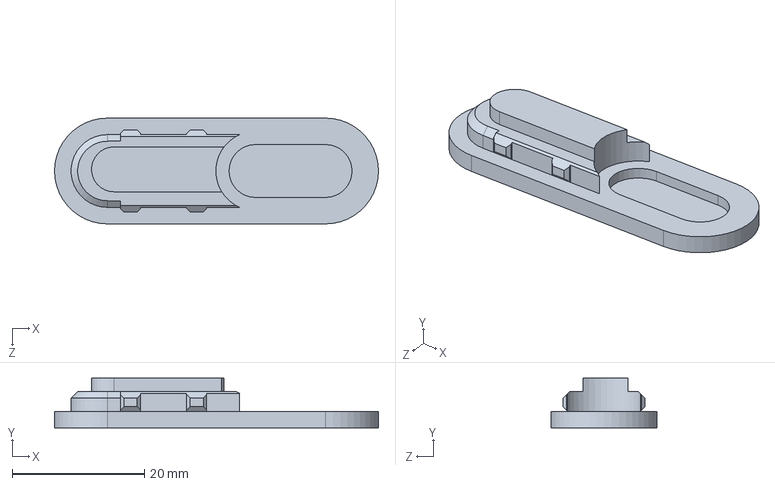
[picture p66: CAD file, 2025-09-27]
结构Rev2N/外壳/推片杆外罩.SLDPRT
49.0 x 7.50 x 16.0 mm
