ZeshuLiu/PolaMiyaHardware/结构Rev2N/片仓总成/片仓地板.SLDPRT

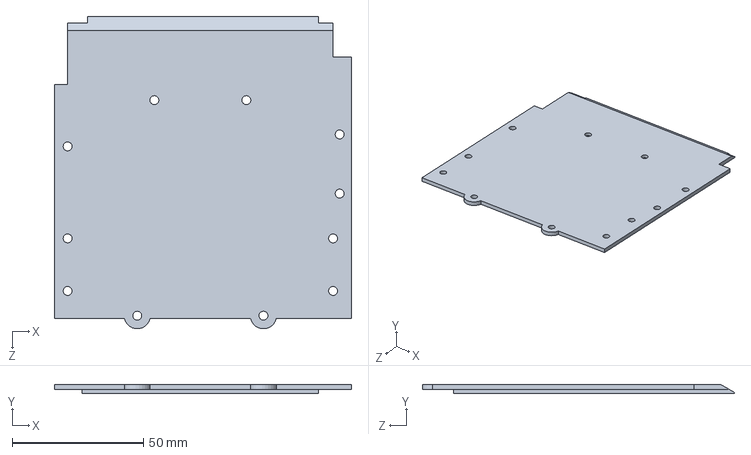
[picture p67: CAD file, 2025-09-27]
结构Rev2N/片仓总成/片仓地板.SLDPRT
113.0 x 3.50 x 118.9 mm
