ZeshuLiu/PolaMiyaHardware/结构Rev2N/片仓总成/电机卡环.SLDPRT

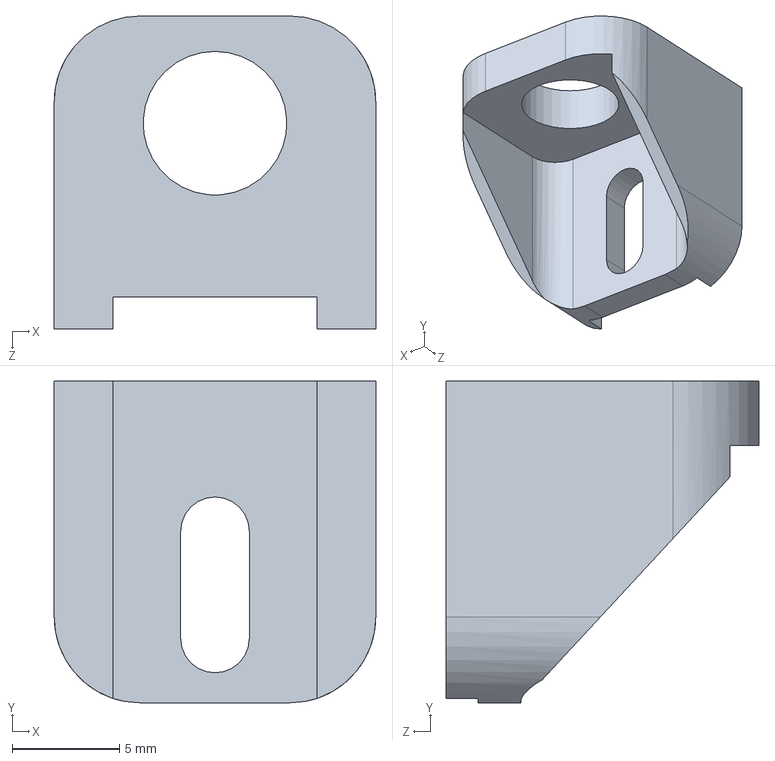
[picture p68: CAD file, 2025-09-27]
结构Rev2N/片仓总成/电机卡环.SLDPRT
15.0 x 15.0 x 14.6 mm
