ZeshuLiu/PolaMiyaHardware/结构Rev2N/片仓总成/主片仓Test2.SLDPRT

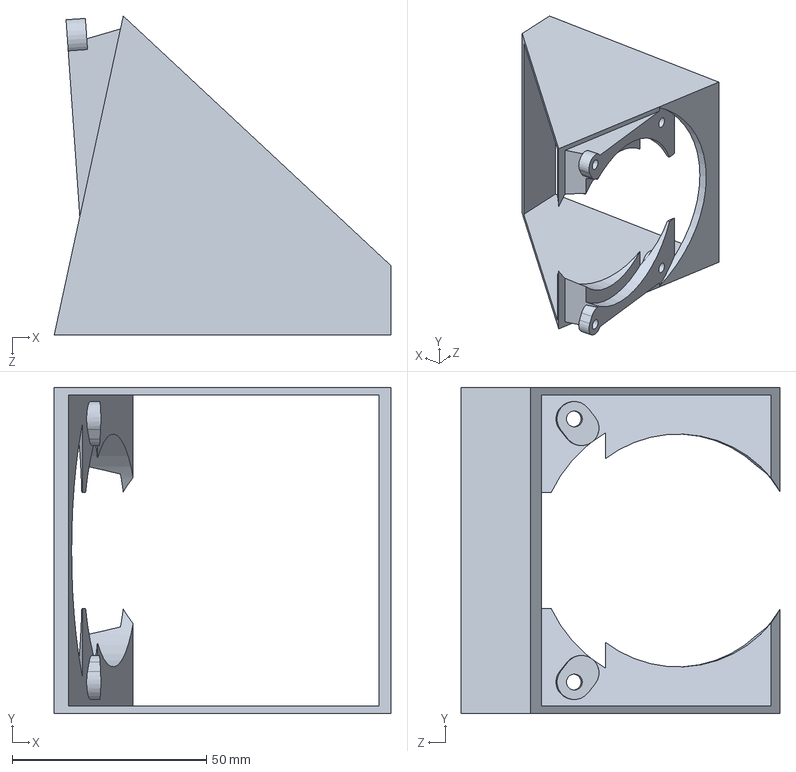
[picture p70: CAD file, 2025-09-27]
结构Rev2N/片仓总成/主片仓Test2.SLDPRT
86.7 x 84.0 x 82.2 mm
