ZeshuLiu/PolaMiyaHardware/结构Rev2N/电路/机身主控/R_1210_3225Metric-6.SLDPRT

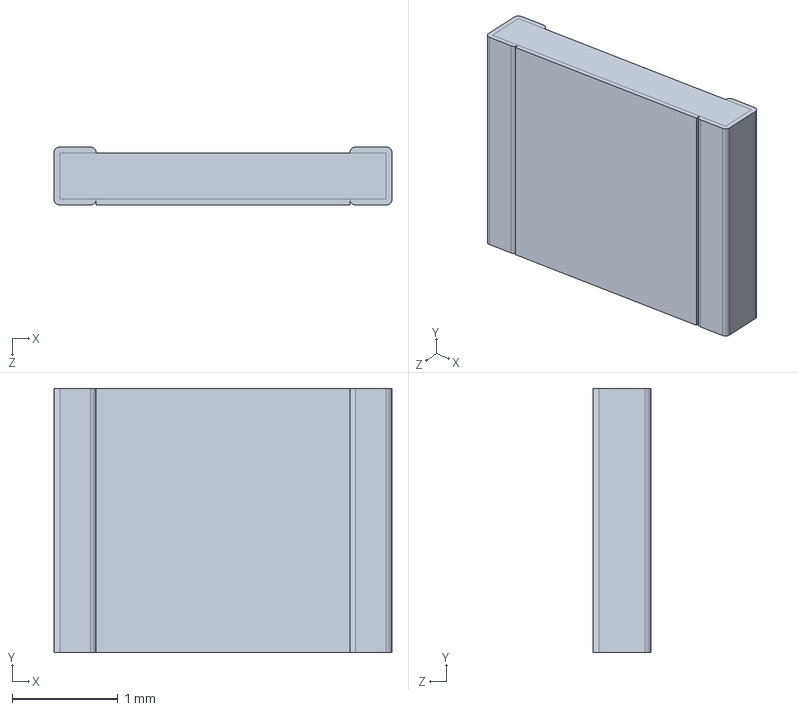
[picture p71: CAD file, 2025-09-27]
结构Rev2N/电路/机身主控/R_1210_3225Metric-6.SLDPRT
3.20 x 2.50 x 0.55 mm
