ZeshuLiu/PolaMiyaHardware/结构Rev2N/片仓总成/开门推杆.SLDPRT

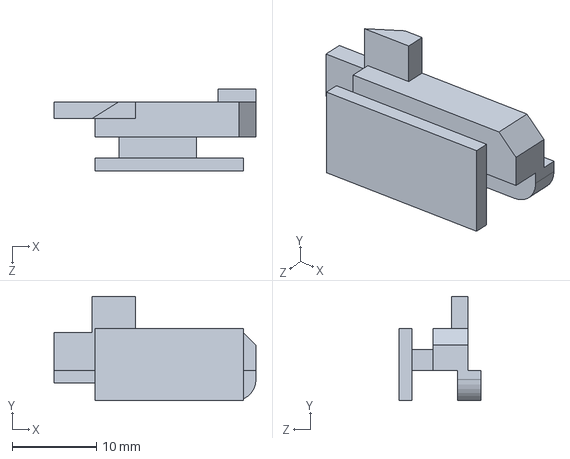
[picture p72: CAD file, 2025-09-27]
结构Rev2N/片仓总成/开门推杆.SLDPRT
24.0 x 12.4 x 9.70 mm
