ZeshuLiu/PolaMiyaHardware/结构Rev2N/片仓总成/推片勾.SLDPRT

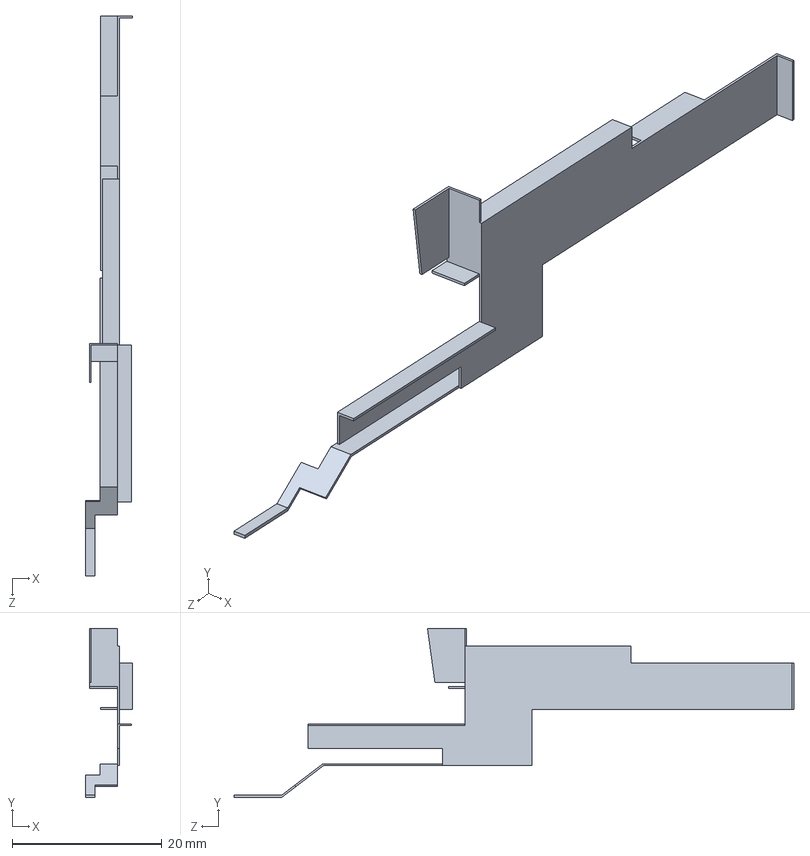
[picture p73: CAD file, 2025-09-27]
结构Rev2N/片仓总成/推片勾.SLDPRT
6.25 x 22.6 x 74.8 mm
