ZeshuLiu/PolaMiyaHardware/结构Rev2N/电路/机身主控/LGA_14_3x25mm_P05mm_LayoutBorder3x4y.SLDPRT

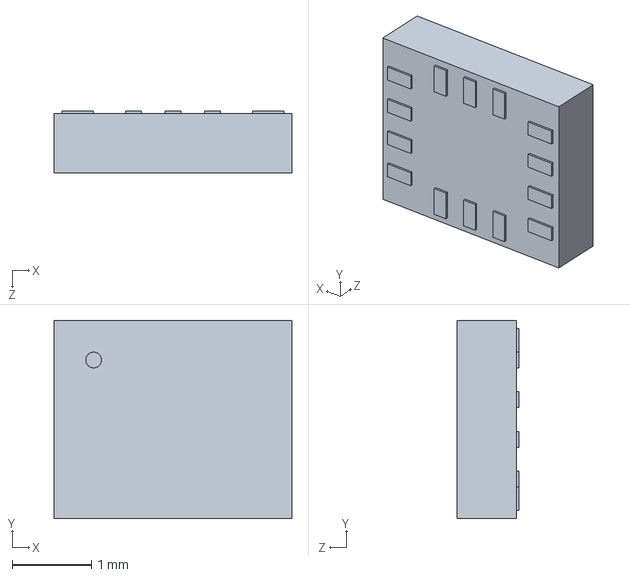
[picture p74: CAD file, 2025-09-27]
结构Rev2N/电路/机身主控/LGA_14_3x25mm_P05mm_LayoutBorder3x4y.SLDPRT
3.00 x 2.50 x 0.78 mm
