ZeshuLiu/PolaMiyaHardware/结构Rev2N/片仓总成/1.6x14.6-拆机.SLDPRT

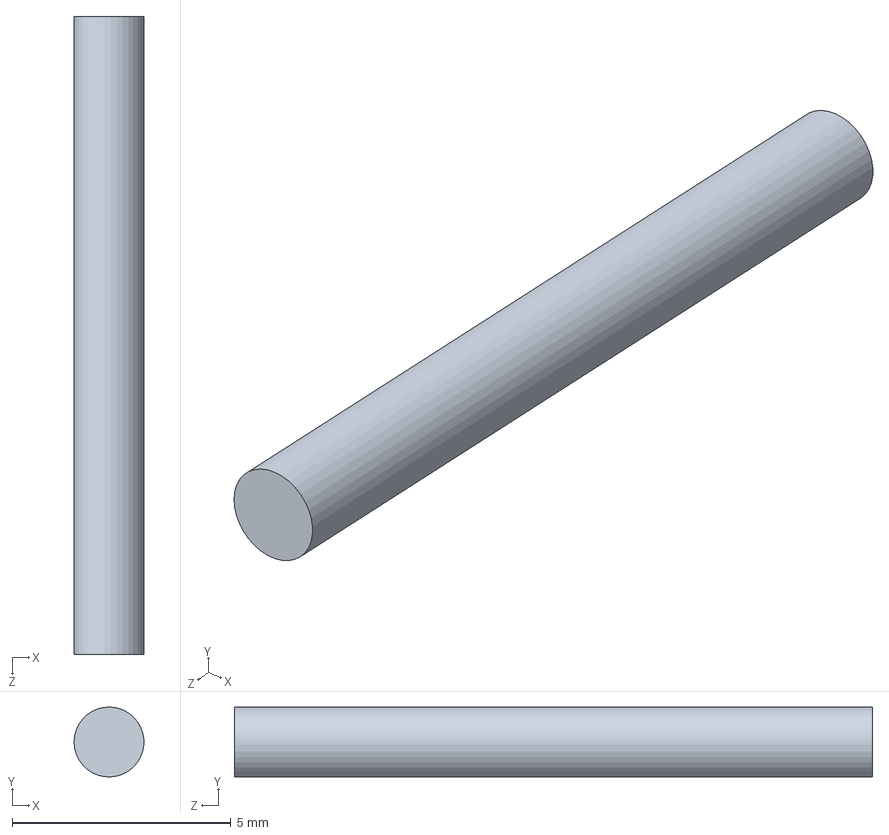
[picture p75: CAD file, 2025-09-27]
结构Rev2N/片仓总成/1.6x14.6-拆机.SLDPRT
1.60 x 1.60 x 14.6 mm
