ZeshuLiu/PolaMiyaHardware/结构Rev2N/片仓总成/推片钩衬垫.SLDPRT

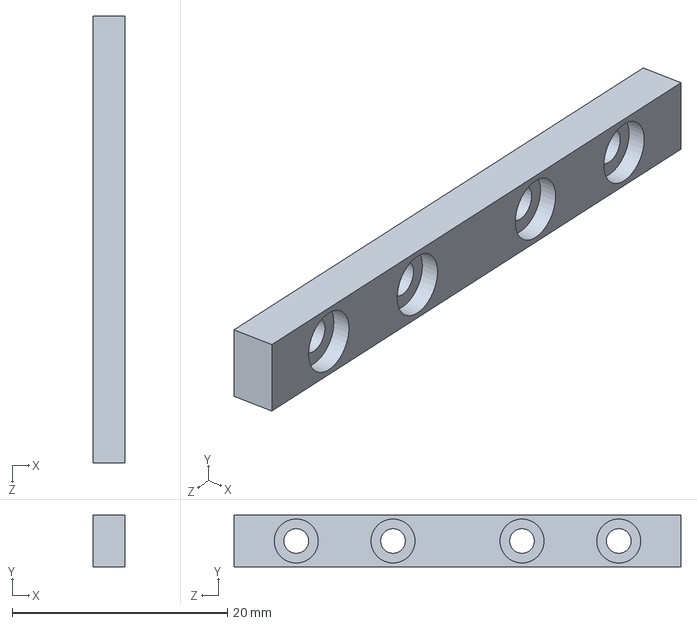
[picture p76: CAD file, 2025-09-27]
结构Rev2N/片仓总成/推片钩衬垫.SLDPRT
3.00 x 4.80 x 41.6 mm
