ZeshuLiu/PolaMiyaHardware/结构Rev2N/片仓总成/侧裙.SLDPRT

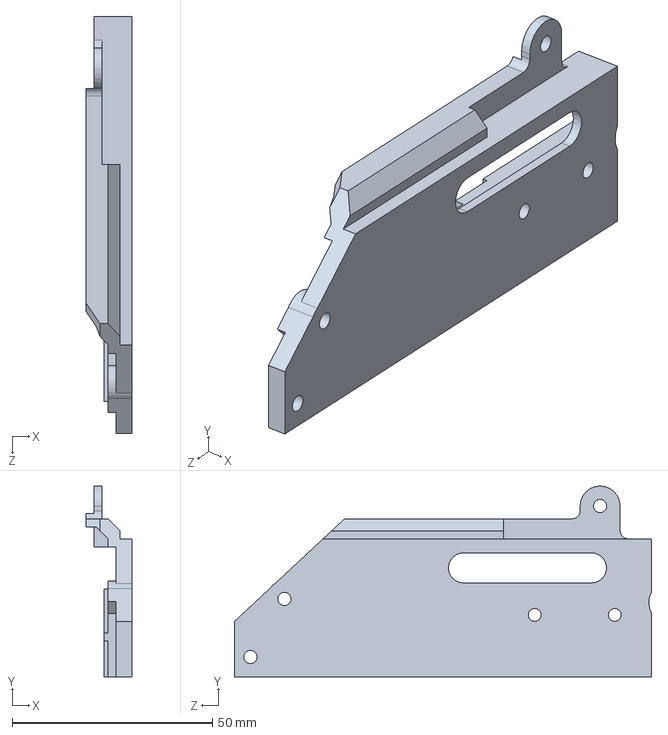
[picture p77: CAD file, 2025-09-27]
结构Rev2N/片仓总成/侧裙.SLDPRT
11.5 x 47.7 x 104.2 mm
