ZeshuLiu/PolaMiyaHardware/结构Rev2N/电路/机身主控/PolamiaPCB.step

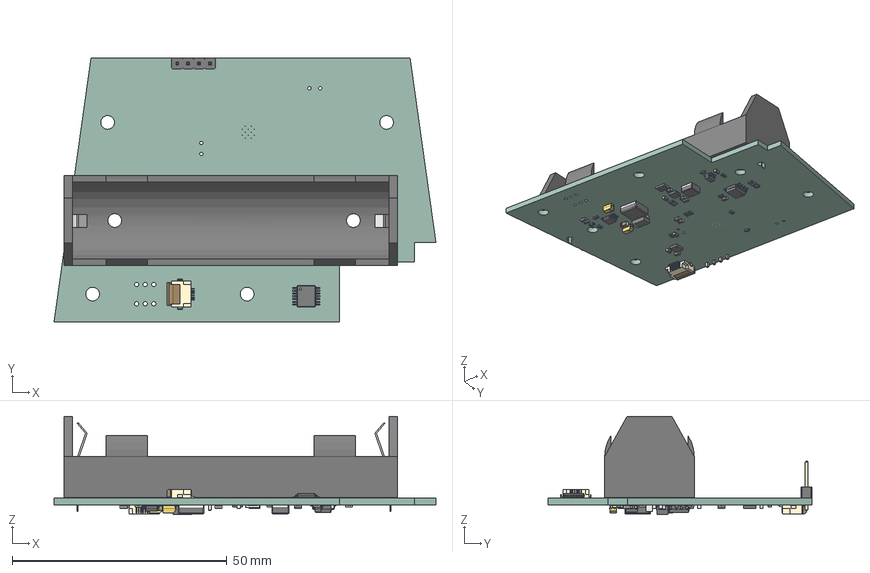
[picture p78: CAD file, 2025-09-27]
结构Rev2N/电路/机身主控/PolamiaPCB.step
89.0 x 61.5 x 22.9 mm
PinHeader_1x04_P254mm_Vertical
TSSOP_14_44x5mm_P065mm
Hirose_FH12_xxS_0_5SH_Parametric_v0_1 x 2
MPD_BH_18650_PC2
R_0603_1608Metric x 16
C_0603_1608Metric x 14
D_SMA
CP_EIA_3216_18_Kemet_A x 2
CQ assembly
VSSOP_8_30x30mm_P065mm
SOIC_8_39x49mm_P127mm
C_0805_2012Metric
SOT_23_6
LGA_14_3x25mm_P05mm_LayoutBorder3x4y
L_Cenker_CKCS6020
R_1210_3225Metric
L_Cenker_CKCS4020
PolamiaPCB_PCB
