ZeshuLiu/PolaMiyaHardware/结构Rev2N/片仓总成/齿轮A-拆机.SLDPRT

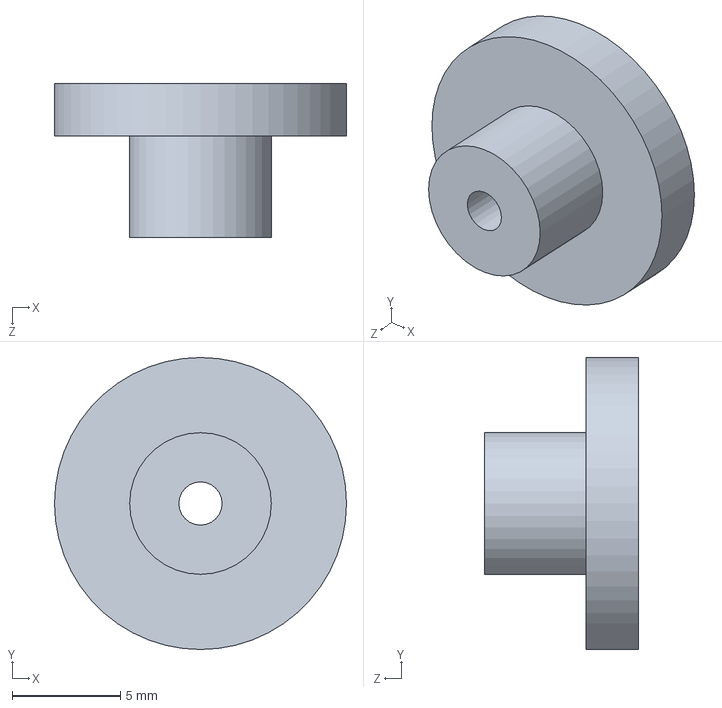
[picture p79: CAD file, 2025-09-27]
结构Rev2N/片仓总成/齿轮A-拆机.SLDPRT
13.5 x 13.5 x 7.14 mm
