ZeshuLiu/PolaMiyaHardware/结构Rev2N/片仓总成/推片把手.SLDPRT

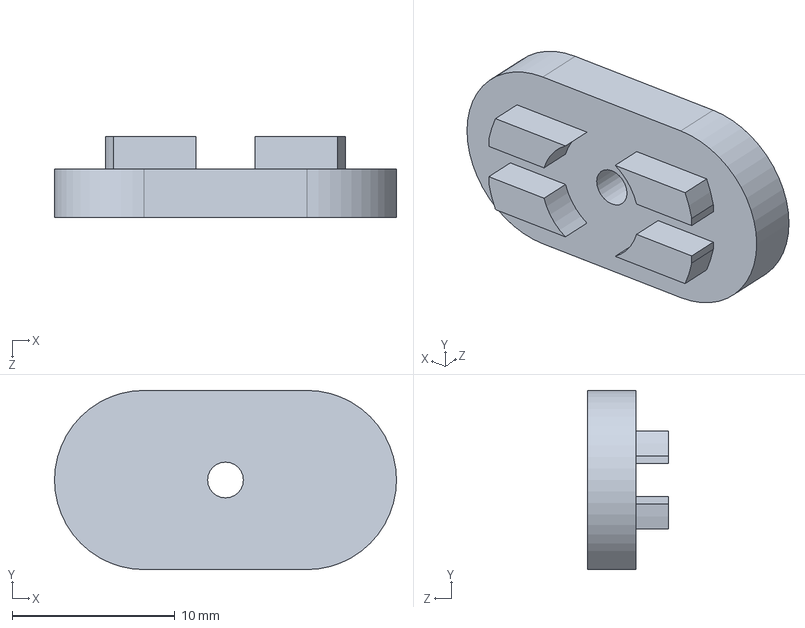
[picture p80: CAD file, 2025-09-27]
结构Rev2N/片仓总成/推片把手.SLDPRT
21.0 x 11.0 x 5.00 mm
