ZeshuLiu/PolaMiyaHardware/结构Rev2N/片仓总成/齿轮维护盖.SLDPRT

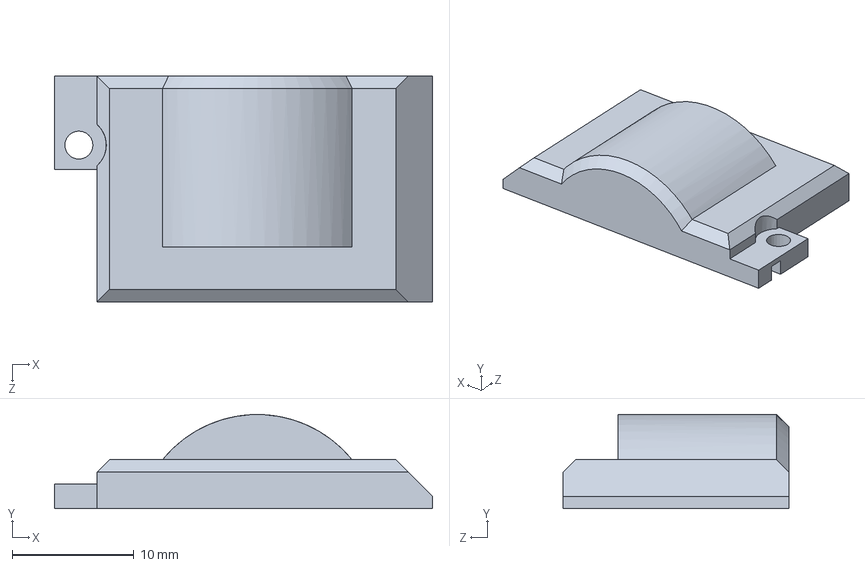
[picture p81: CAD file, 2025-09-27]
结构Rev2N/片仓总成/齿轮维护盖.SLDPRT
31.0 x 7.71 x 18.5 mm
