ZeshuLiu/PolaMiyaHardware/结构Rev2N/电路/机身主控/L_Cenker_CKCS6020-4.SLDPRT

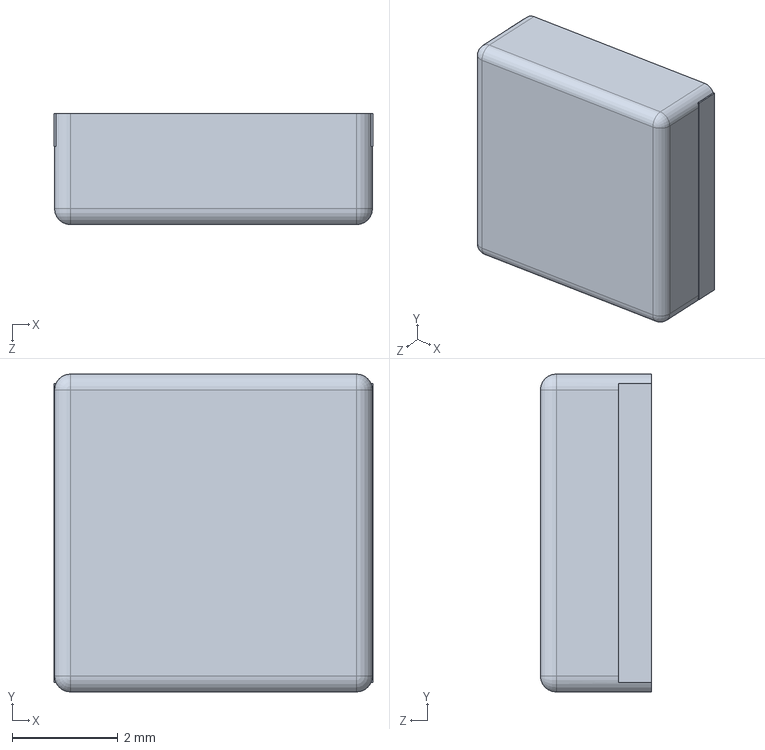
[picture p82: CAD file, 2025-09-27]
结构Rev2N/电路/机身主控/L_Cenker_CKCS6020-4.SLDPRT
6.02 x 6.00 x 2.10 mm
