ZeshuLiu/PolaMiyaHardware/结构Rev2N/片仓总成/吐片钣金固定销.SLDPRT

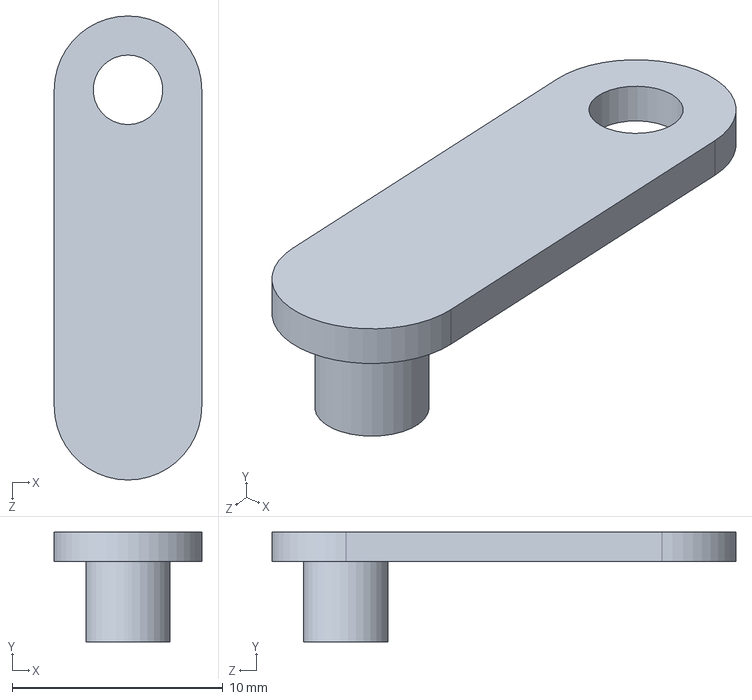
[picture p83: CAD file, 2025-09-27]
结构Rev2N/片仓总成/吐片钣金固定销.SLDPRT
7.00 x 5.20 x 22.0 mm
