ZeshuLiu/PolaMiyaHardware/结构Rev2N/片仓总成/MG825-拆机.SLDPRT

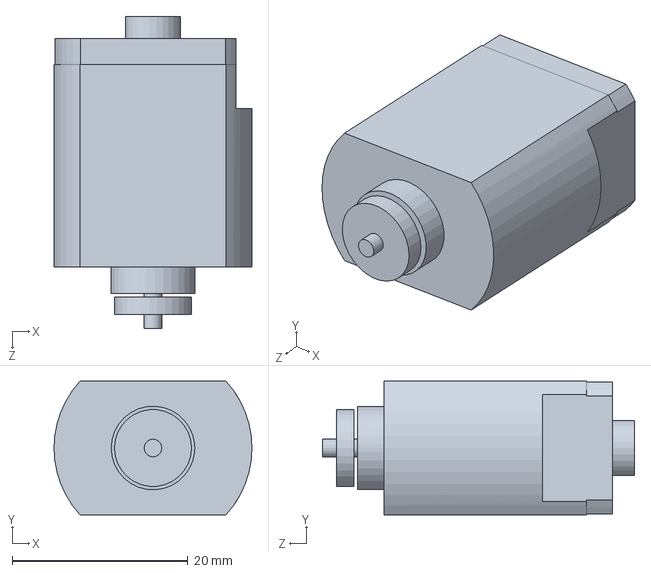
[picture p84: CAD file, 2025-09-27]
结构Rev2N/片仓总成/MG825-拆机.SLDPRT
22.5 x 15.2 x 35.5 mm
