ZeshuLiu/PolaMiyaHardware/结构Rev2N/片仓总成/相纸盒.SLDPRT

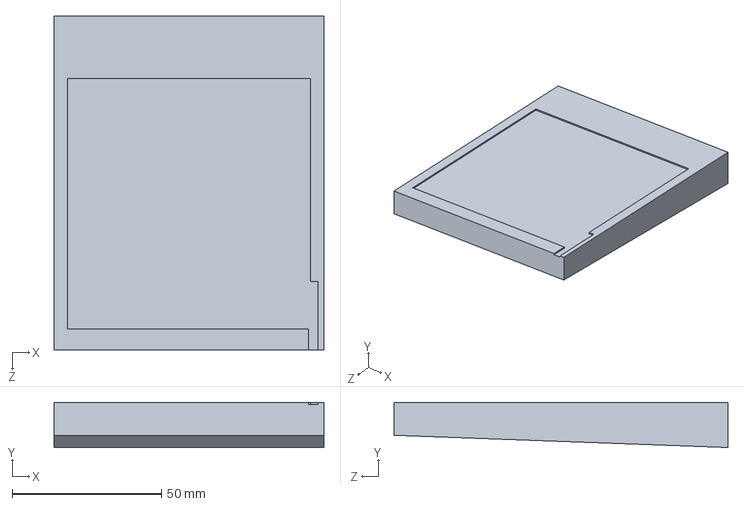
[picture p85: CAD file, 2025-09-27]
结构Rev2N/片仓总成/相纸盒.SLDPRT
90.5 x 15.1 x 112.0 mm
