ZeshuLiu/PolaMiyaHardware/结构Rev2N/电路/机身主控/PolamiaPCB_PCB.SLDPRT

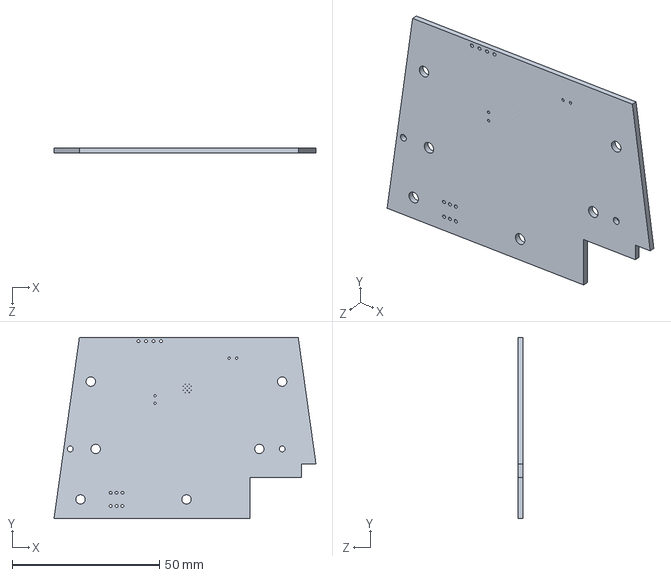
[picture p86: CAD file, 2025-09-27]
结构Rev2N/电路/机身主控/PolamiaPCB_PCB.SLDPRT
89.0 x 61.5 x 1.61 mm
