ZeshuLiu/PolaMiyaHardware/结构Rev2N/片仓总成/齿轮C-拆机.SLDPRT

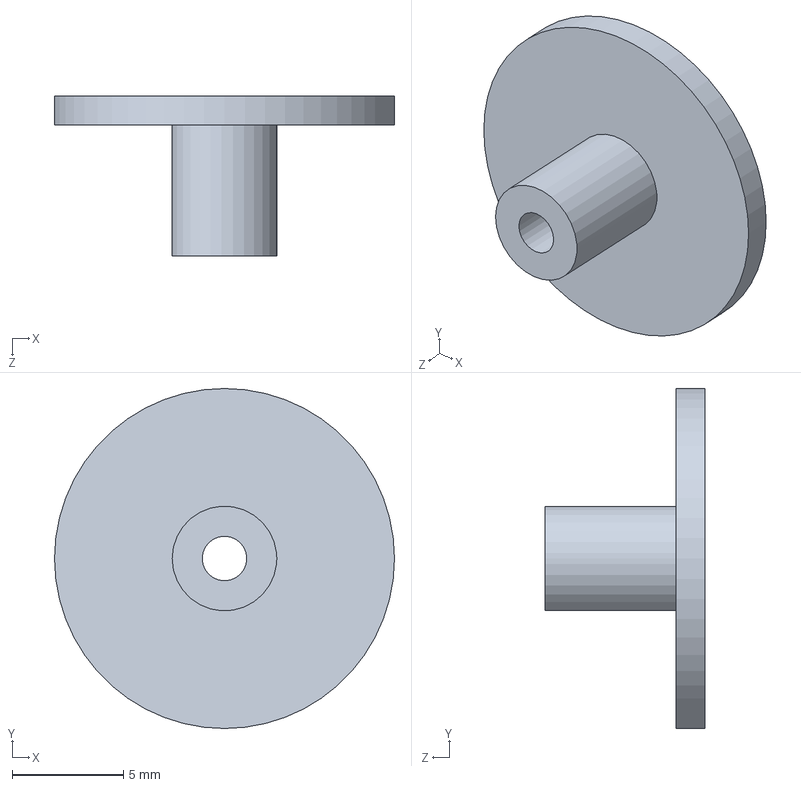
[picture p87: CAD file, 2025-09-27]
结构Rev2N/片仓总成/齿轮C-拆机.SLDPRT
15.3 x 15.3 x 7.20 mm
