ZeshuLiu/PolaMiyaHardware/结构Rev2N/片仓总成/前盖板.SLDPRT

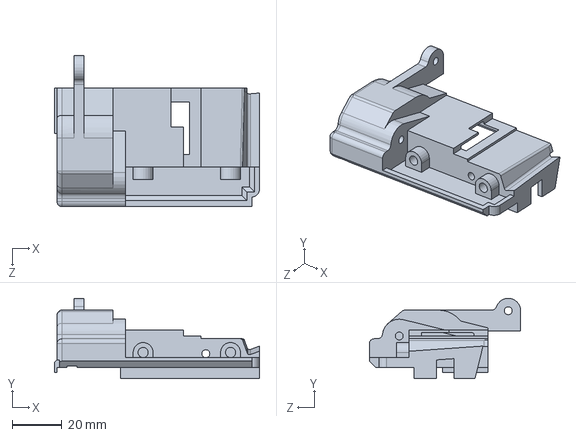
[picture p88: CAD file, 2025-09-27]
结构Rev2N/片仓总成/前盖板.SLDPRT
82.1 x 32.2 x 60.7 mm
