ZeshuLiu/PolaMiyaHardware/结构Rev2N/电路/机身主控/MPD_BH_18650_PC2.SLDPRT

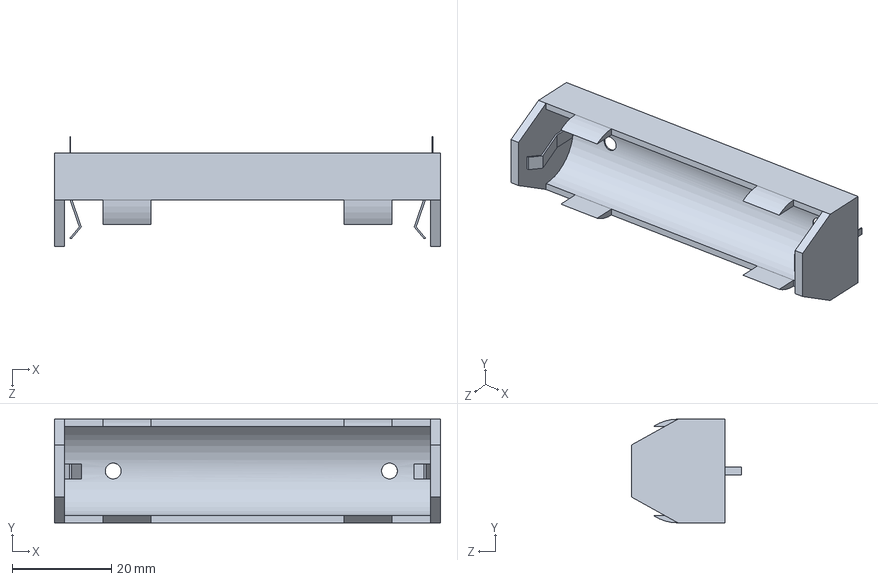
[picture p89: CAD file, 2025-09-27]
结构Rev2N/电路/机身主控/MPD_BH_18650_PC2.SLDPRT
77.7 x 20.9 x 22.2 mm
