ZeshuLiu/PolaMiyaHardware/结构Rev2N/片仓总成/吐片口机身钣金-拆机.SLDPRT

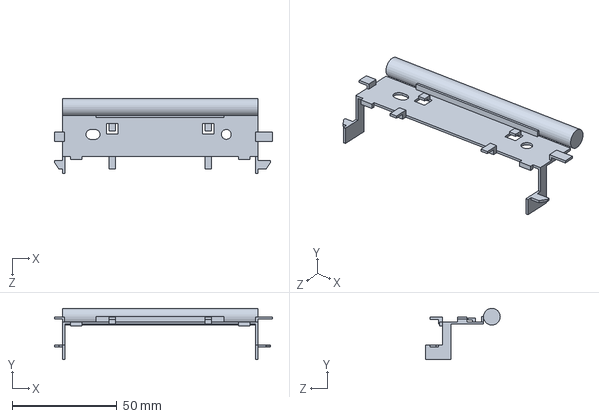
[picture p90: CAD file, 2025-09-27]
结构Rev2N/片仓总成/吐片口机身钣金-拆机.SLDPRT
103.8 x 24.5 x 35.5 mm
