ZeshuLiu/PolaMiyaHardware/结构Rev2N/片仓总成/出片推杆.SLDPRT

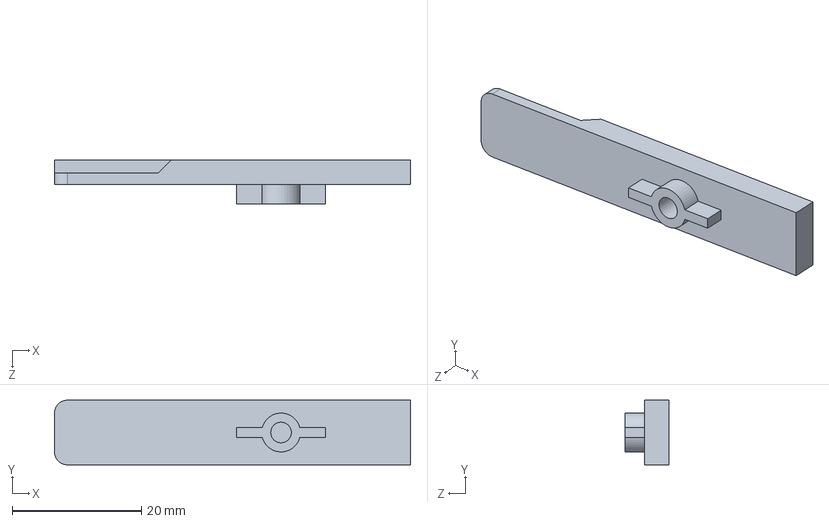
[picture p91: CAD file, 2025-09-27]
结构Rev2N/片仓总成/出片推杆.SLDPRT
55.0 x 10.0 x 6.75 mm
