ZeshuLiu/PolaMiyaHardware/结构Rev2N/片仓总成/主片仓Test3.SLDPRT

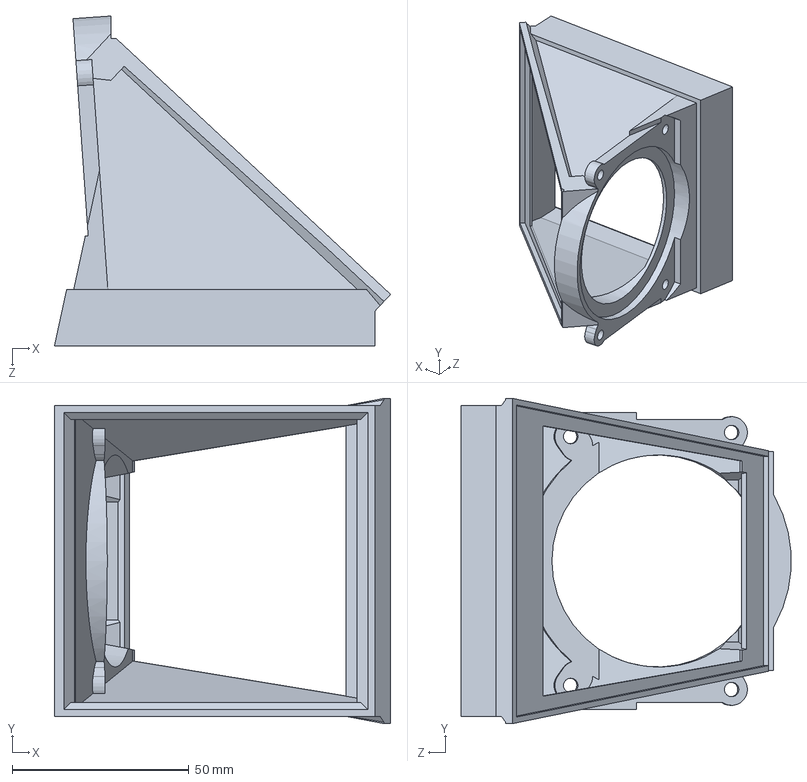
[picture p93: CAD file, 2025-09-27]
结构Rev2N/片仓总成/主片仓Test3.SLDPRT
95.2 x 92.1 x 93.4 mm
