ZeshuLiu/PolaMiyaHardware/结构Rev2N/片仓总成/推杆外框.SLDPRT

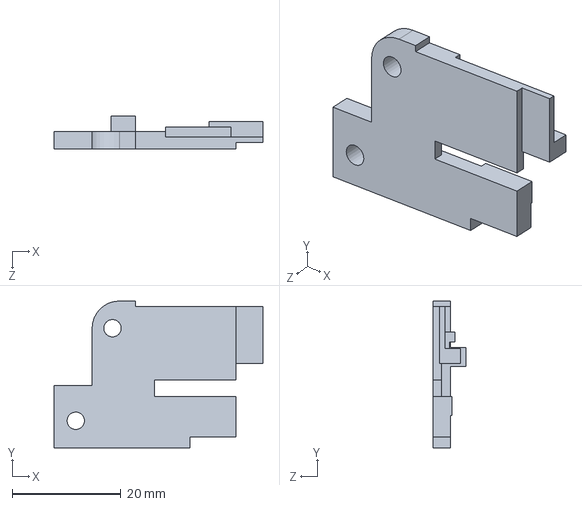
[picture p94: CAD file, 2025-09-27]
结构Rev2N/片仓总成/推杆外框.SLDPRT
38.4 x 27.0 x 6.00 mm
