ZeshuLiu/PolaMiyaHardware/结构Rev2N/电路/机身主控/SOIC_8_39x49mm_P127mm.SLDPRT

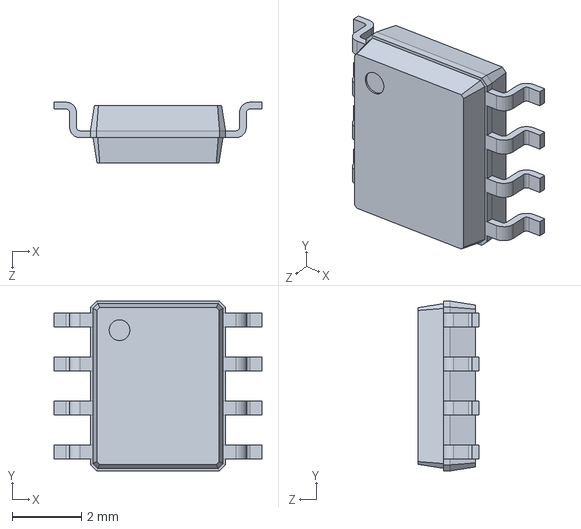
[picture p95: CAD file, 2025-09-27]
结构Rev2N/电路/机身主控/SOIC_8_39x49mm_P127mm.SLDPRT
6.00 x 4.90 x 1.75 mm
