ZeshuLiu/PolaMiyaHardware/结构Rev2N/片仓总成/齿轮D-拆机.SLDPRT

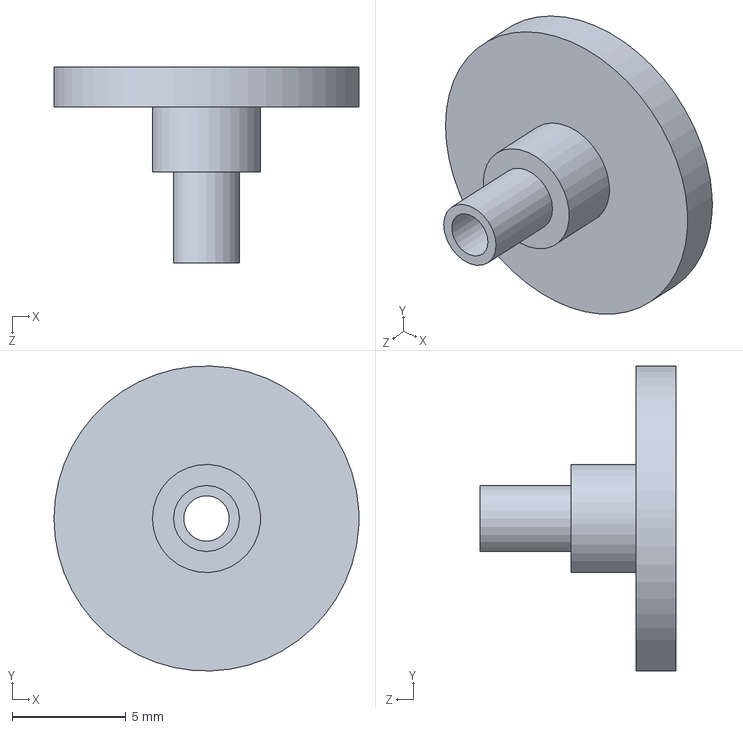
[picture p96: CAD file, 2025-09-27]
结构Rev2N/片仓总成/齿轮D-拆机.SLDPRT
13.4 x 13.4 x 8.60 mm
