ZeshuLiu/PolaMiyaHardware/结构Rev2N/片仓总成/齿轮盖.SLDPRT

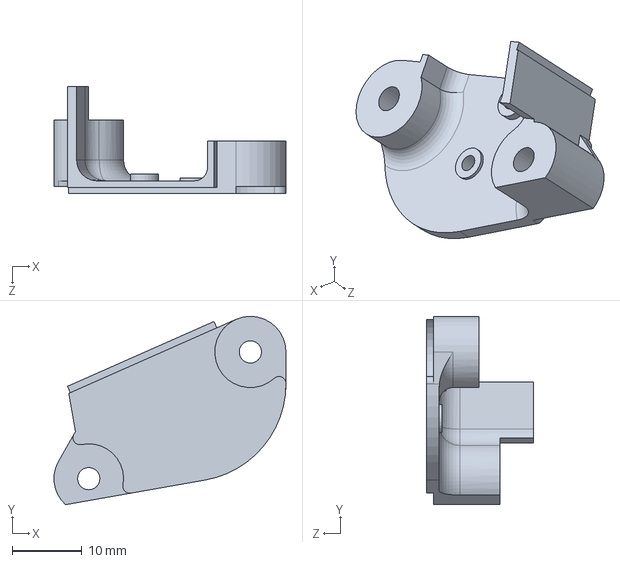
[picture p97: CAD file, 2025-09-27]
结构Rev2N/片仓总成/齿轮盖.SLDPRT
33.3 x 27.0 x 15.3 mm
