ZeshuLiu/PolaMiyaHardware/结构Rev2N/片仓总成/主片仓Test1.SLDPRT

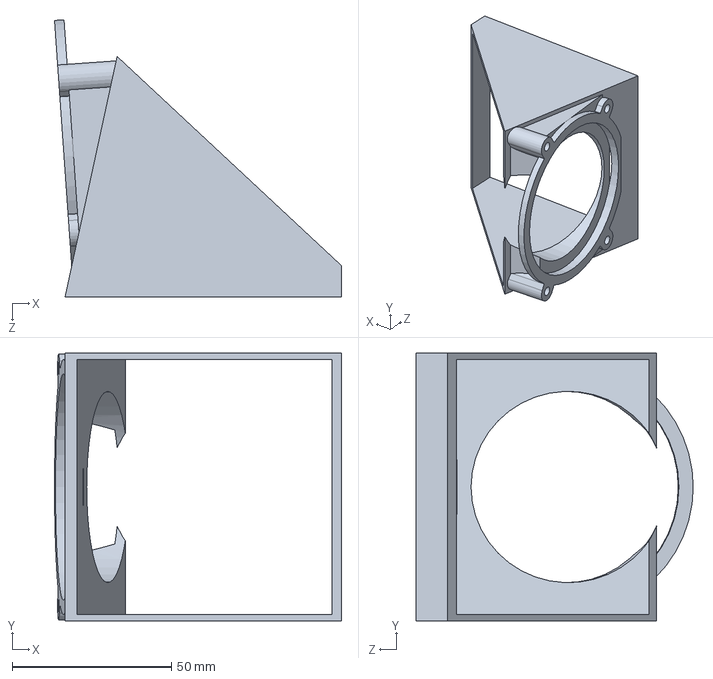
[picture p99: CAD file, 2025-09-27]
结构Rev2N/片仓总成/主片仓Test1.SLDPRT
90.0 x 84.0 x 87.0 mm
