ZeshuLiu/PolaMiyaHardware/结构Rev2N/片仓总成/主反射镜.SLDPRT

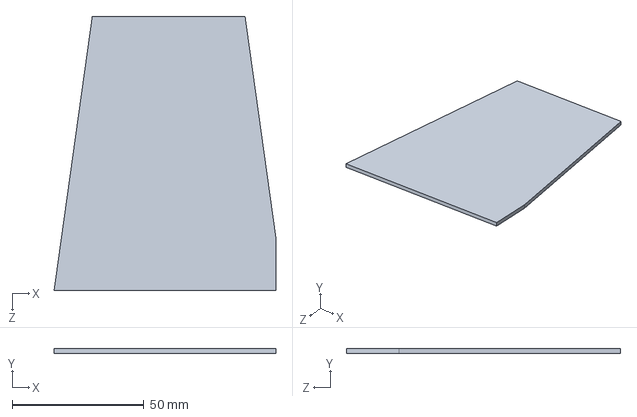
[picture p100: CAD file, 2025-09-27]
结构Rev2N/片仓总成/主反射镜.SLDPRT
84.2 x 1.80 x 104.0 mm
