ZeshuLiu/PolaMiyaHardware/结构Rev2N/电路/机身主控/D_SMA-2.SLDPRT

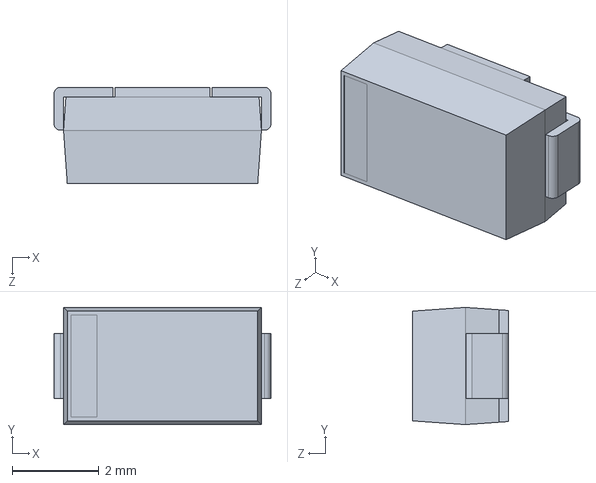
[picture p101: CAD file, 2025-09-27]
结构Rev2N/电路/机身主控/D_SMA-2.SLDPRT
5.00 x 2.70 x 2.22 mm
