ZeshuLiu/PolaMiyaHardware/结构Rev2N/片仓总成/齿轮B-拆机.SLDPRT

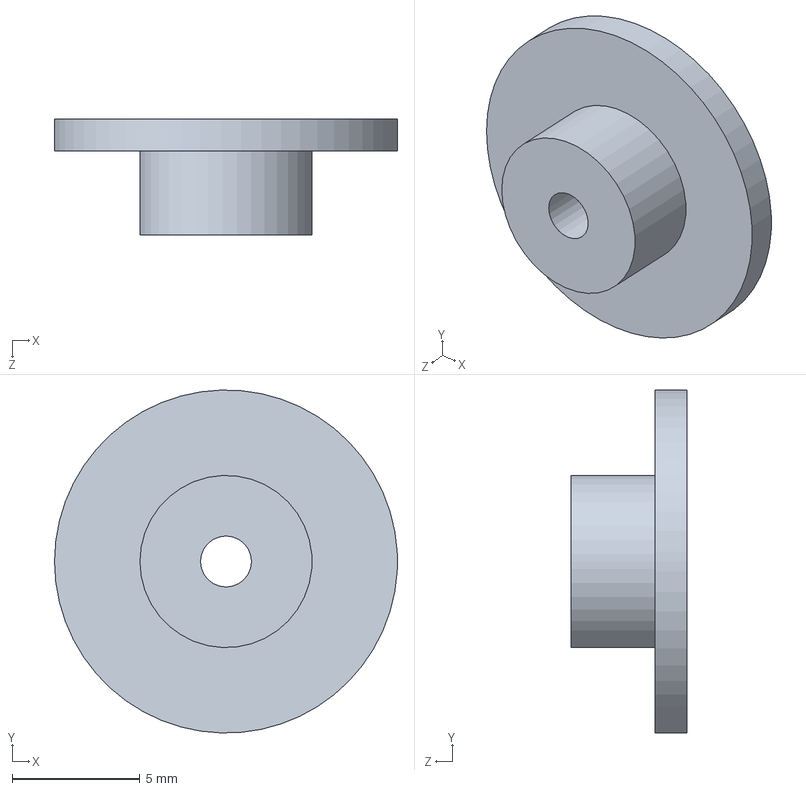
[picture p102: CAD file, 2025-09-27]
结构Rev2N/片仓总成/齿轮B-拆机.SLDPRT
13.5 x 13.4 x 4.55 mm
