ZeshuLiu/PolaMiyaHardware/结构Rev2N/电路/机身主控/PinHeader_1x04_P254mm_Vertical.SLDPRT

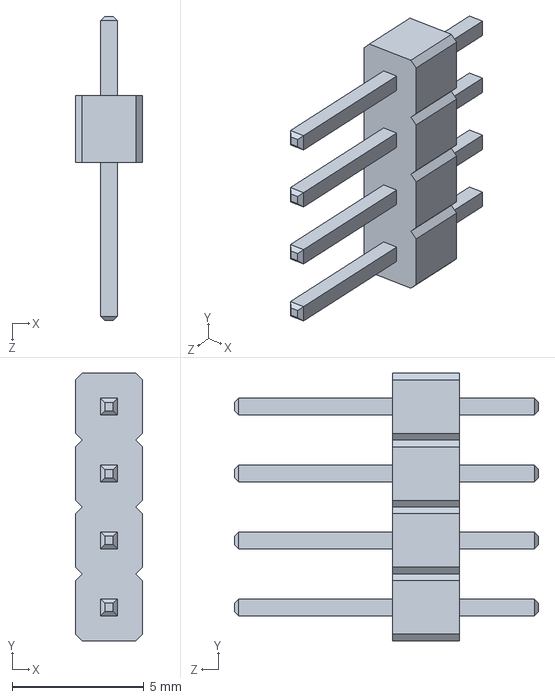
[picture p103: CAD file, 2025-09-27]
结构Rev2N/电路/机身主控/PinHeader_1x04_P254mm_Vertical.SLDPRT
2.54 x 10.2 x 11.5 mm
