ZeshuLiu/PolaMiyaHardware/结构Rev2N/片仓总成/电池壳.SLDPRT

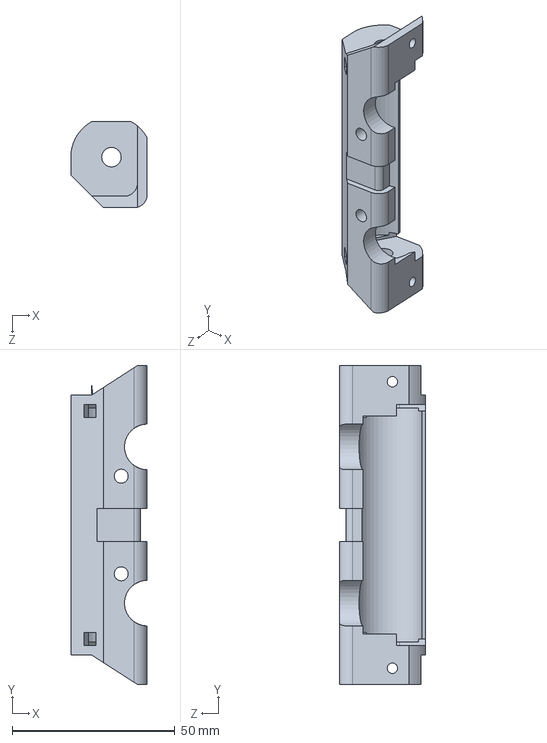
[picture p104: CAD file, 2025-09-27]
结构Rev2N/片仓总成/电池壳.SLDPRT
23.5 x 98.0 x 26.5 mm
