ZeshuLiu/PolaMiyaHardware/结构Rev2N/电路/机身主控/Hirose_FH12_xxS_0_5SH_Parametric_v0_1-5.SLDPRT

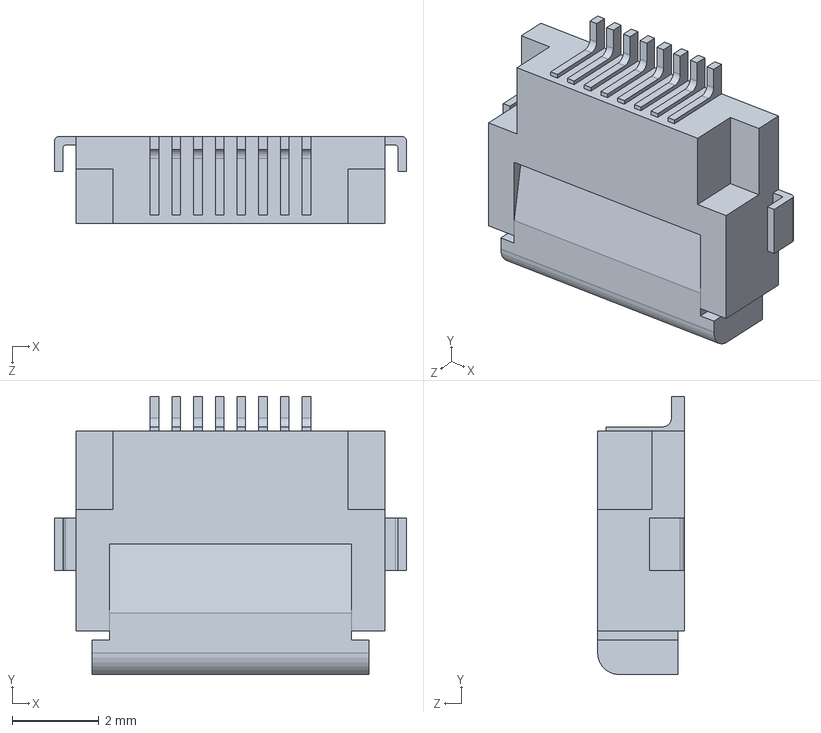
[picture p105: CAD file, 2025-09-27]
结构Rev2N/电路/机身主控/Hirose_FH12_xxS_0_5SH_Parametric_v0_1-5.SLDPRT
8.10 x 6.40 x 2.00 mm
