ZeshuLiu/PolaMiyaHardware/结构Rev2N/片仓总成/片仓弹簧.SLDPRT

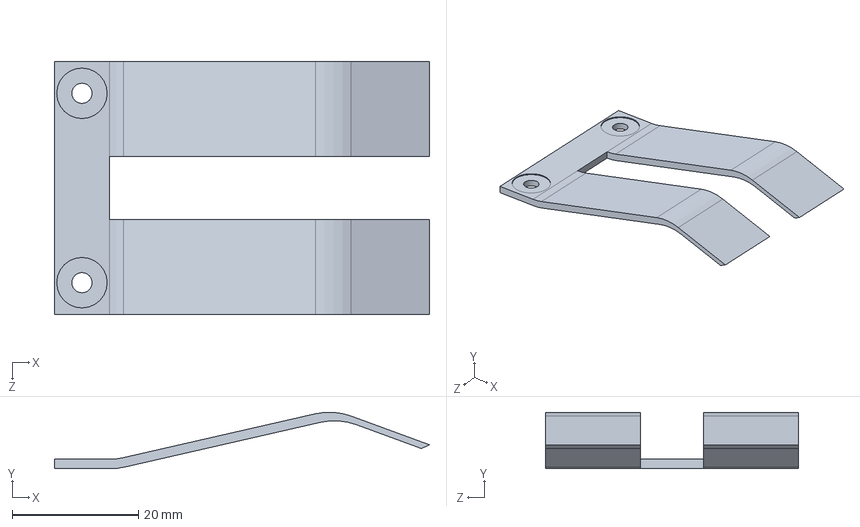
[picture p106: CAD file, 2025-09-27]
结构Rev2N/片仓总成/片仓弹簧.SLDPRT
59.4 x 8.93 x 40.0 mm
